mrheltic/Logger/medias/doc-esp32-pinout-reference-wroom-devkit.png

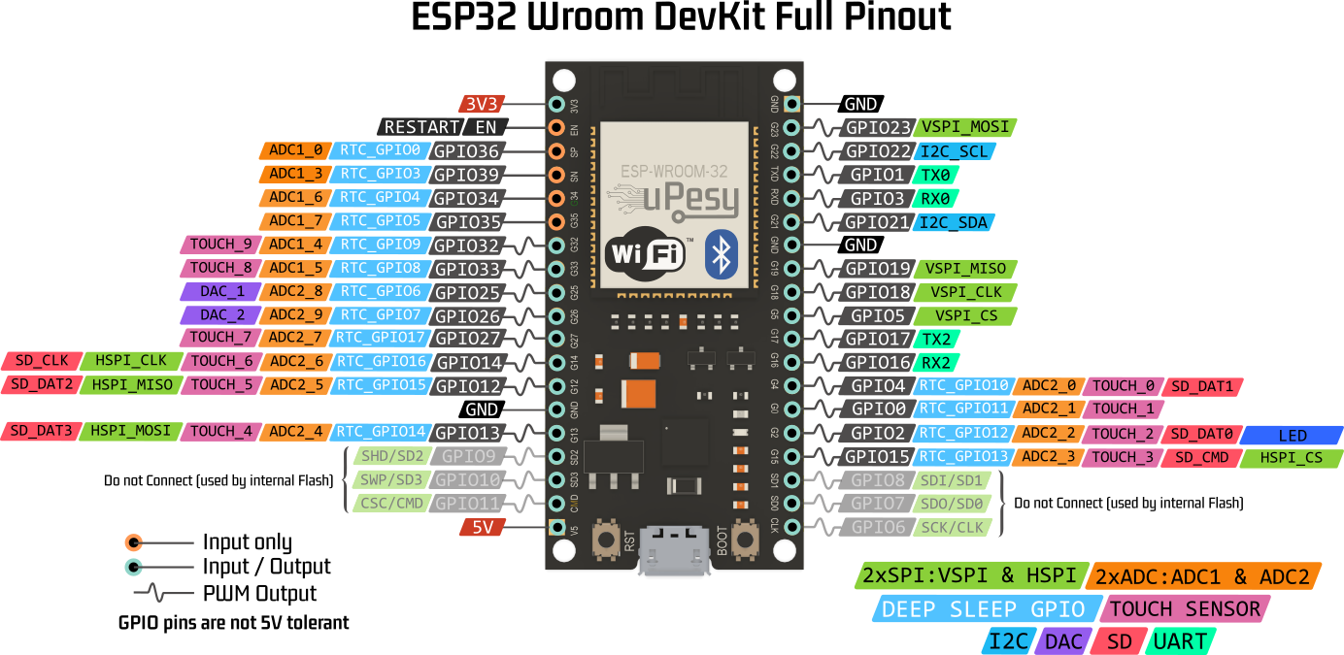
medias/doc-esp32-pinout-reference-wroom-devkit.png
