mrheltic/Logger/medias/kicad_logger_circuit.jpg

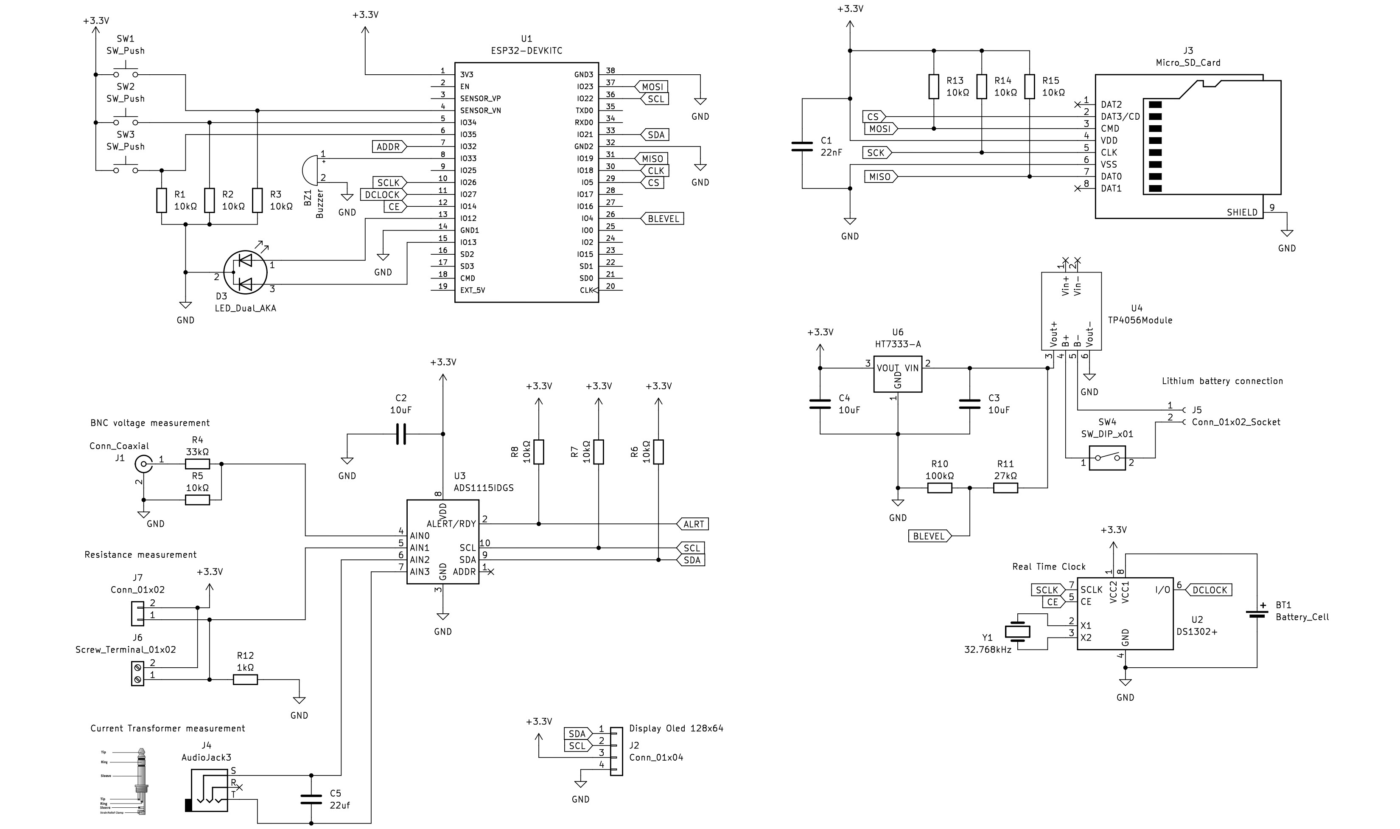
medias/kicad_logger_circuit.jpg
