mrheltic/Logger/medias/pcb_preview_bottom.png

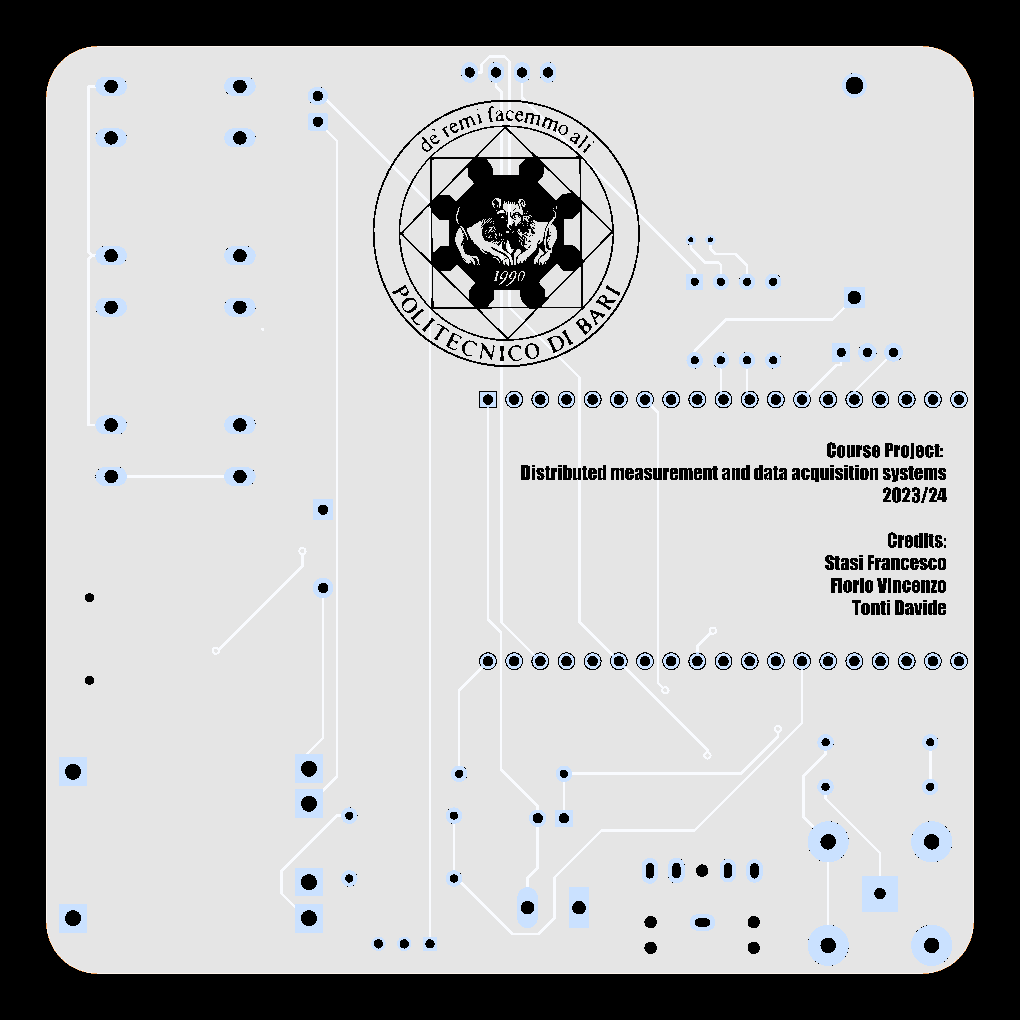
medias/pcb_preview_bottom.png
