mrheltic/Logger/medias/pcb_preview_top.png

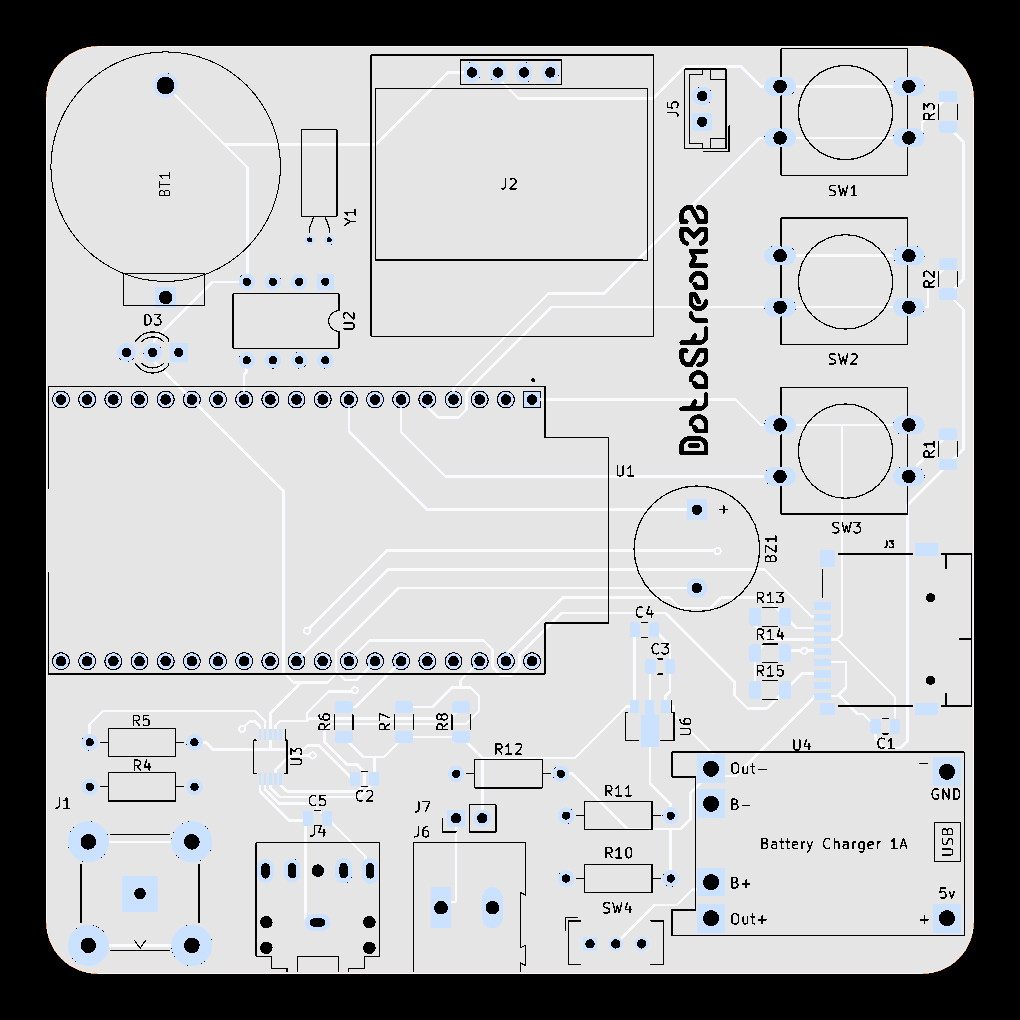
medias/pcb_preview_top.png
