mrheltic/Logger/Performance/Calibration/calibration.png

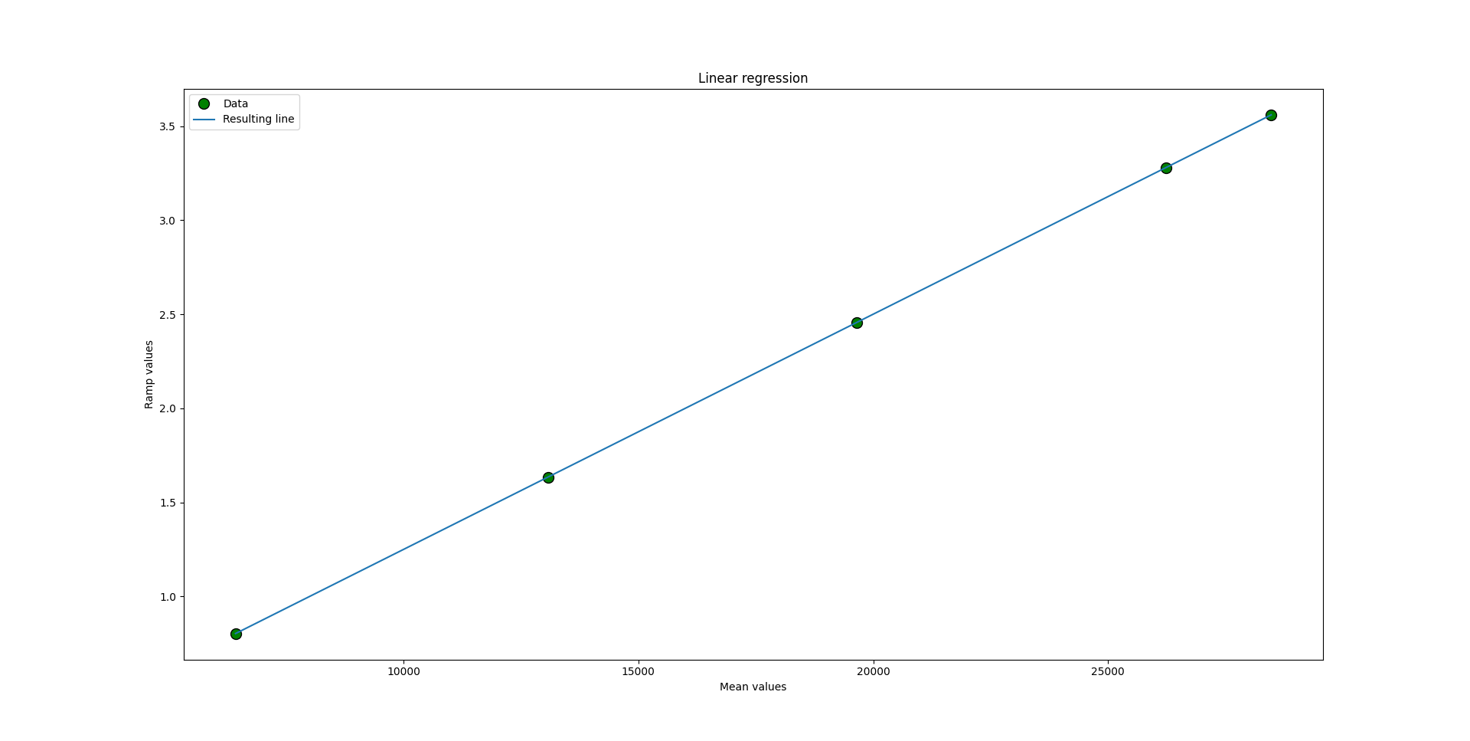
Performance/Calibration/calibration.png
