mrheltic/Logger/Performance/Fft/rampfft2.png

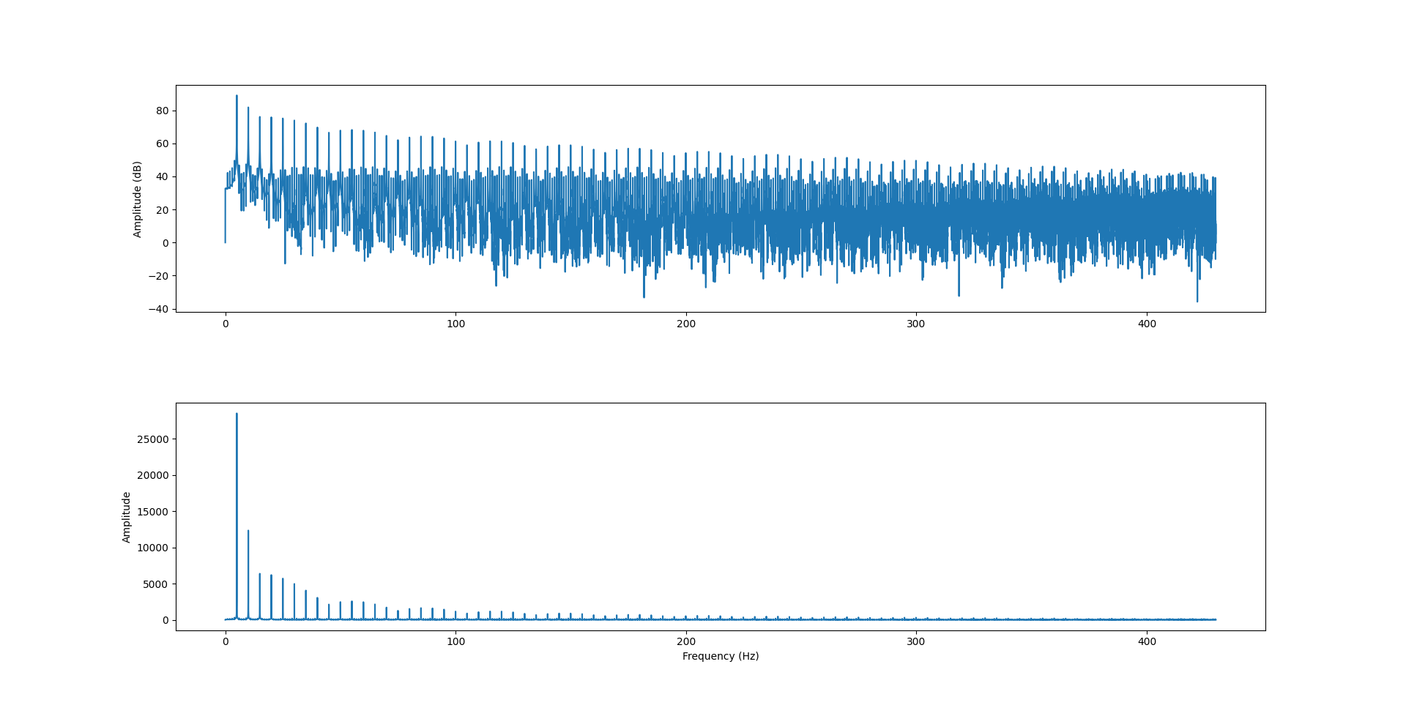
Performance/Fft/rampfft2.png
