mrheltic/Logger/Performance/Fft/sinusoidalfft1.png

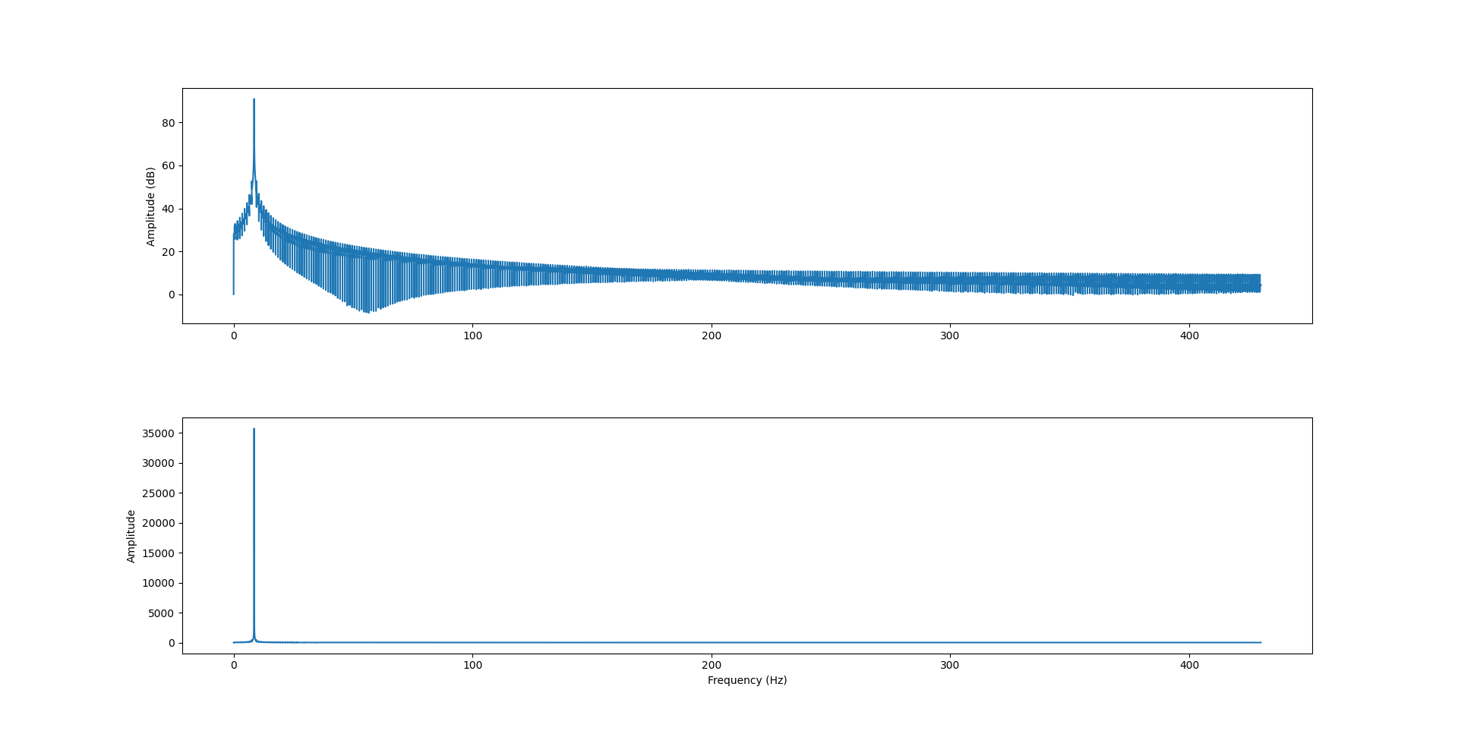
Performance/Fft/sinusoidalfft1.png
