mrheltic/Logger/Performance/Fft/sinusoidalfft2.png

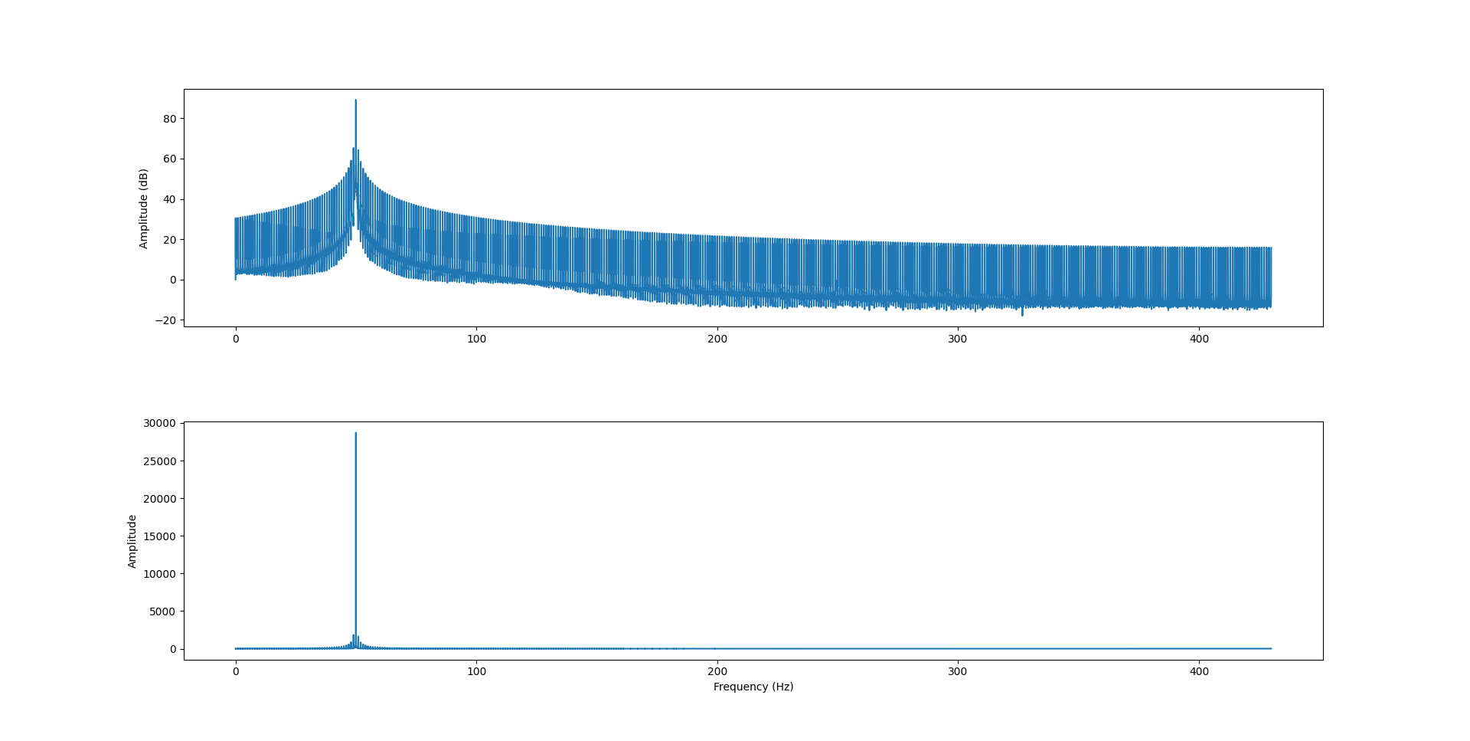
Performance/Fft/sinusoidalfft2.png
