mrheltic/Logger/Performance/Fft/sinusoidalfft4.png

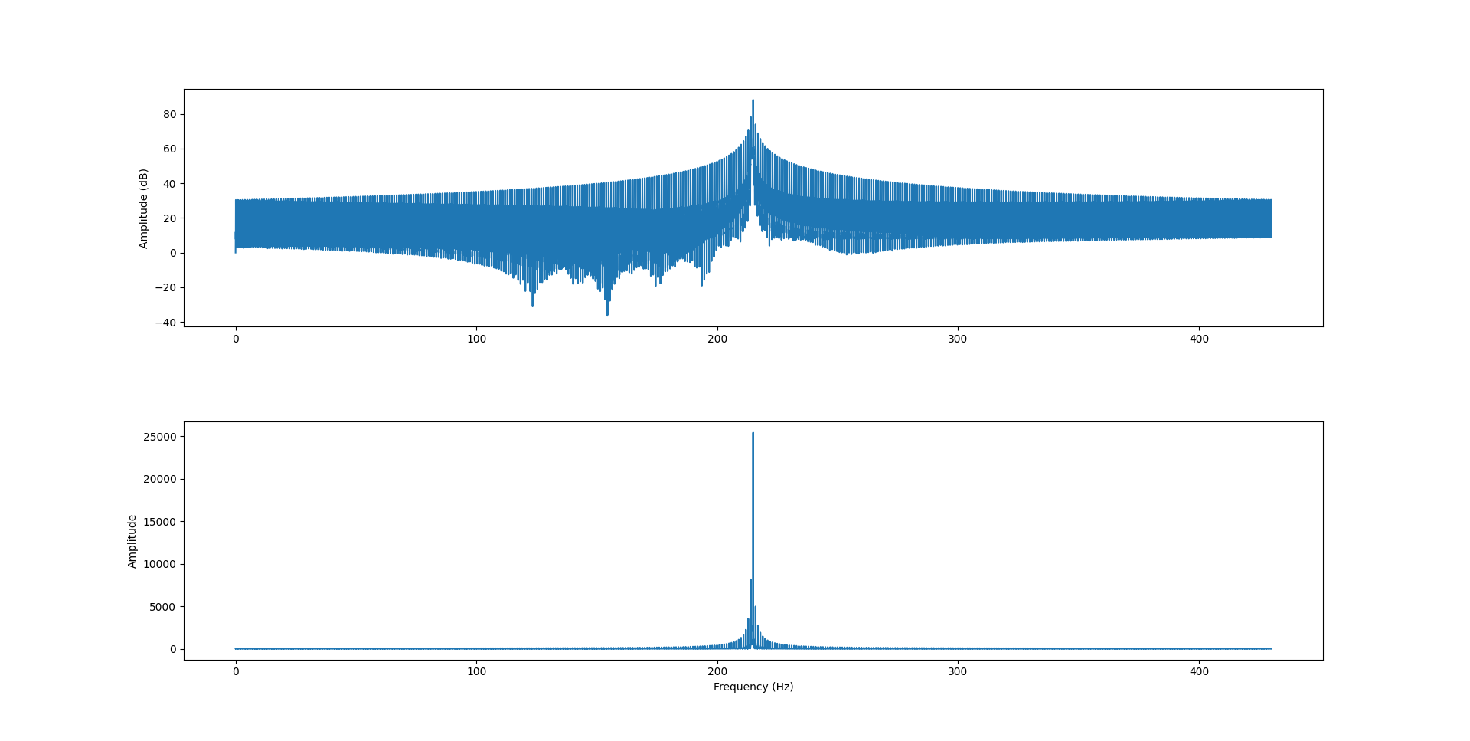
Performance/Fft/sinusoidalfft4.png
