mrheltic/Logger/Performance/Fft/sinusoidalfft6.png

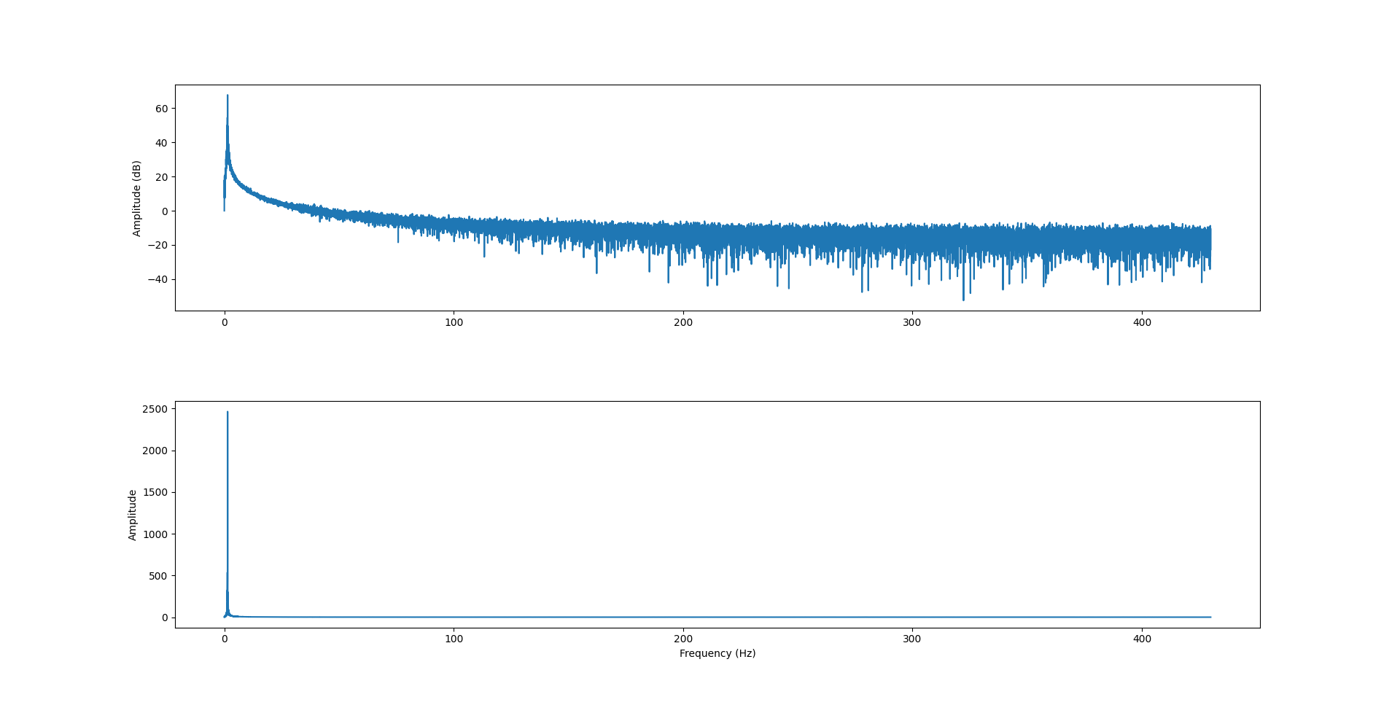
Performance/Fft/sinusoidalfft6.png
