mrheltic/Logger/Performance/Fft/sinusoidalfft8.png

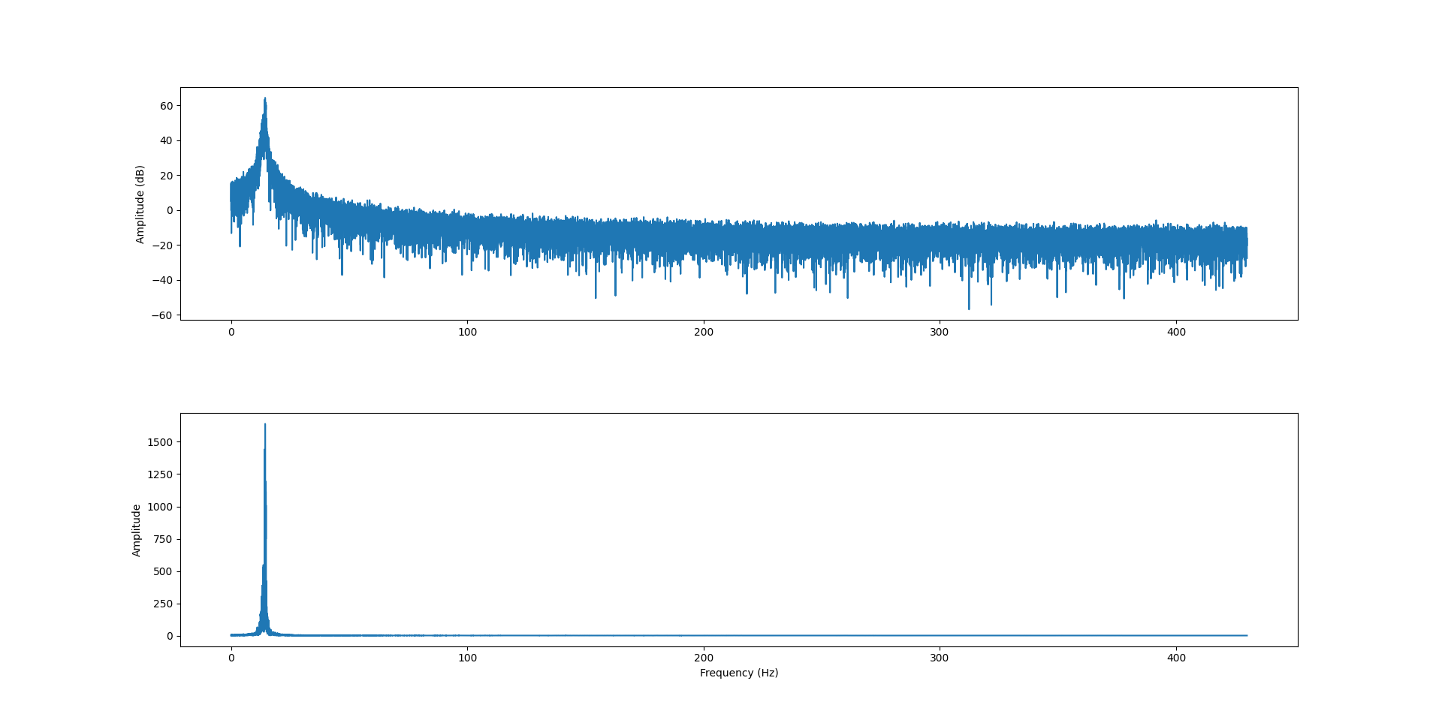
Performance/Fft/sinusoidalfft8.png
