mrheltic/Logger/Performance/Fft/sinusoidalfft9.png

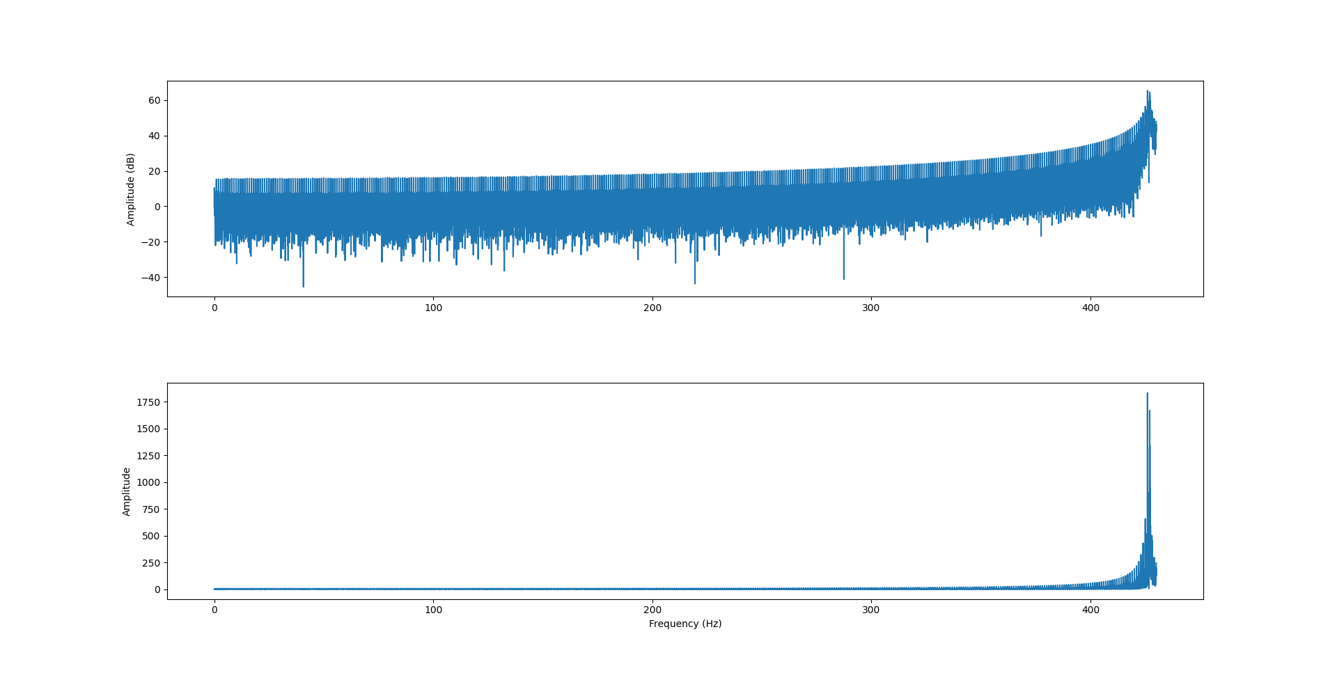
Performance/Fft/sinusoidalfft9.png
