mrheltic/Logger/Performance/Noise/floatingnoise.png

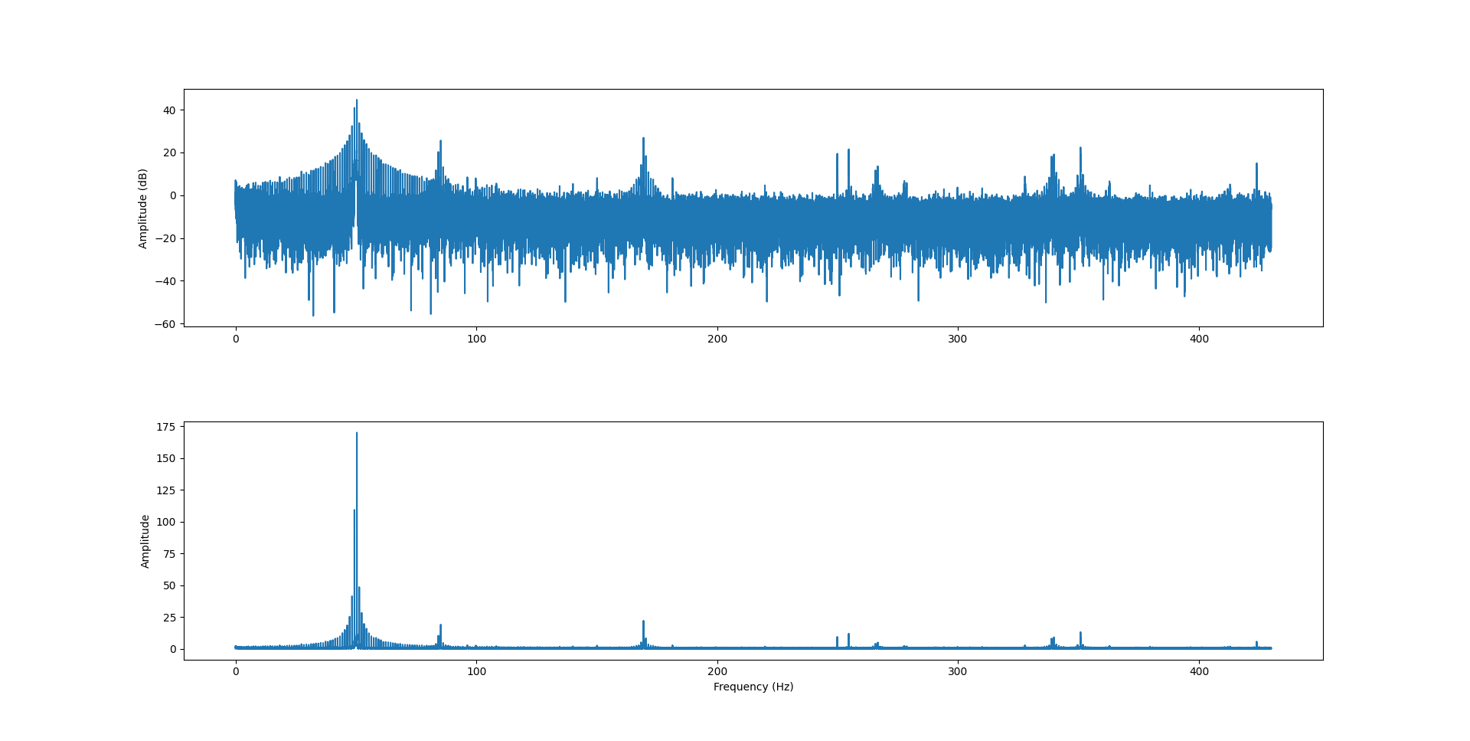
Performance/Noise/floatingnoise.png
