mrheltic/Logger/Performance/Noise/shortingnoise.png

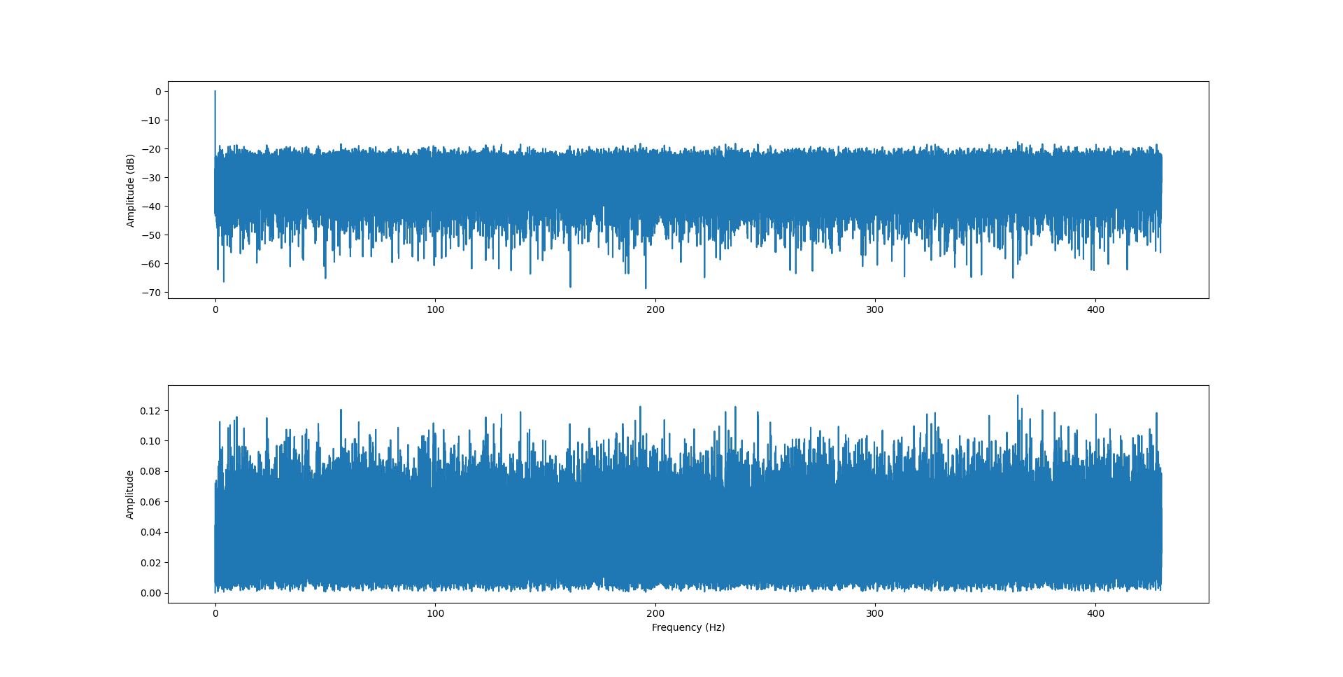
Performance/Noise/shortingnoise.png
