mrheltic/Logger/Performance/Ramp/rampfit1.png

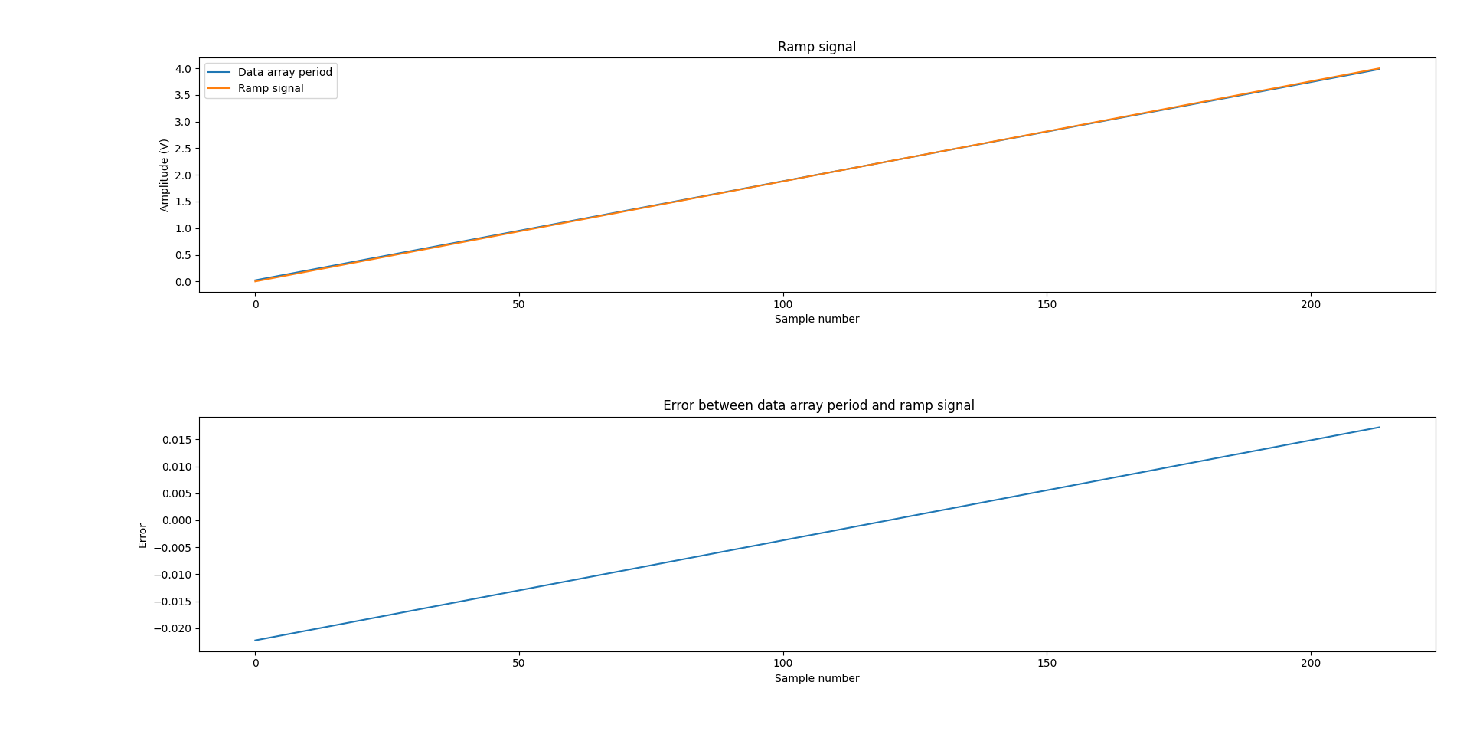
Performance/Ramp/rampfit1.png
