mrheltic/Logger/Performance/Ramp/rampfsr1.png

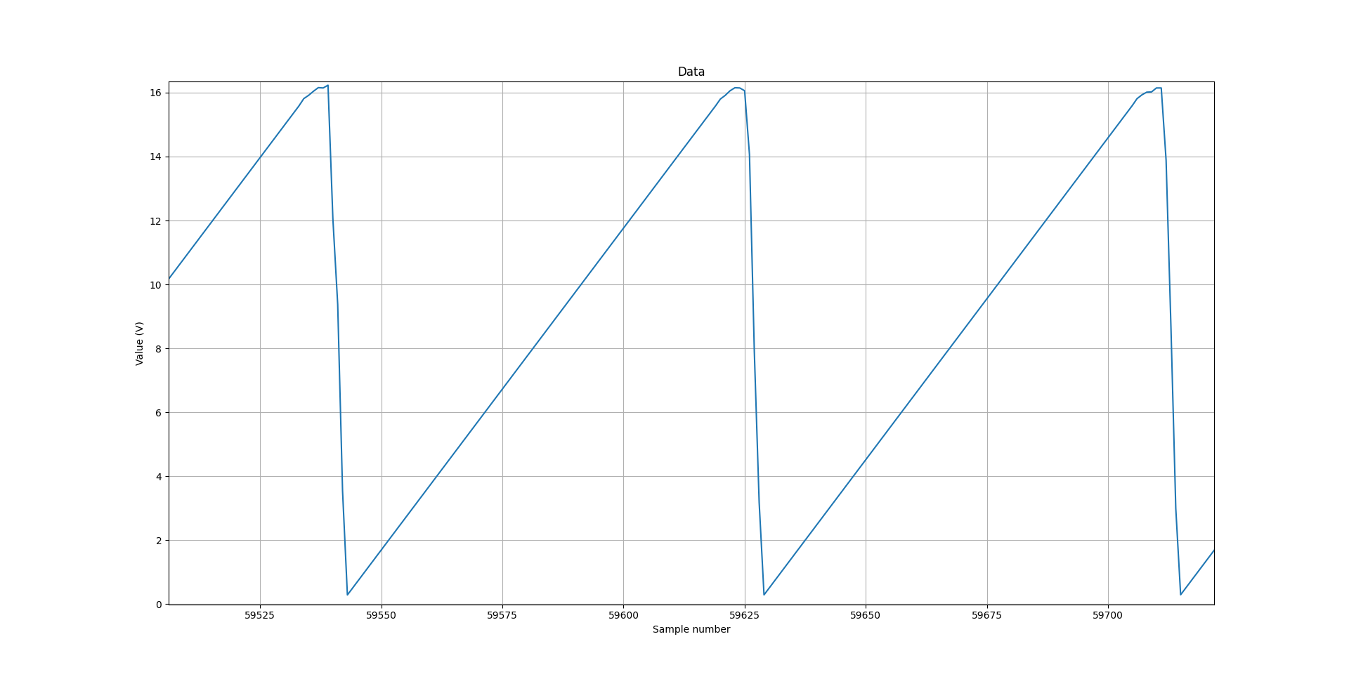
Performance/Ramp/rampfsr1.png
