mrheltic/Logger/Performance/Ramp/rampfsr2.png

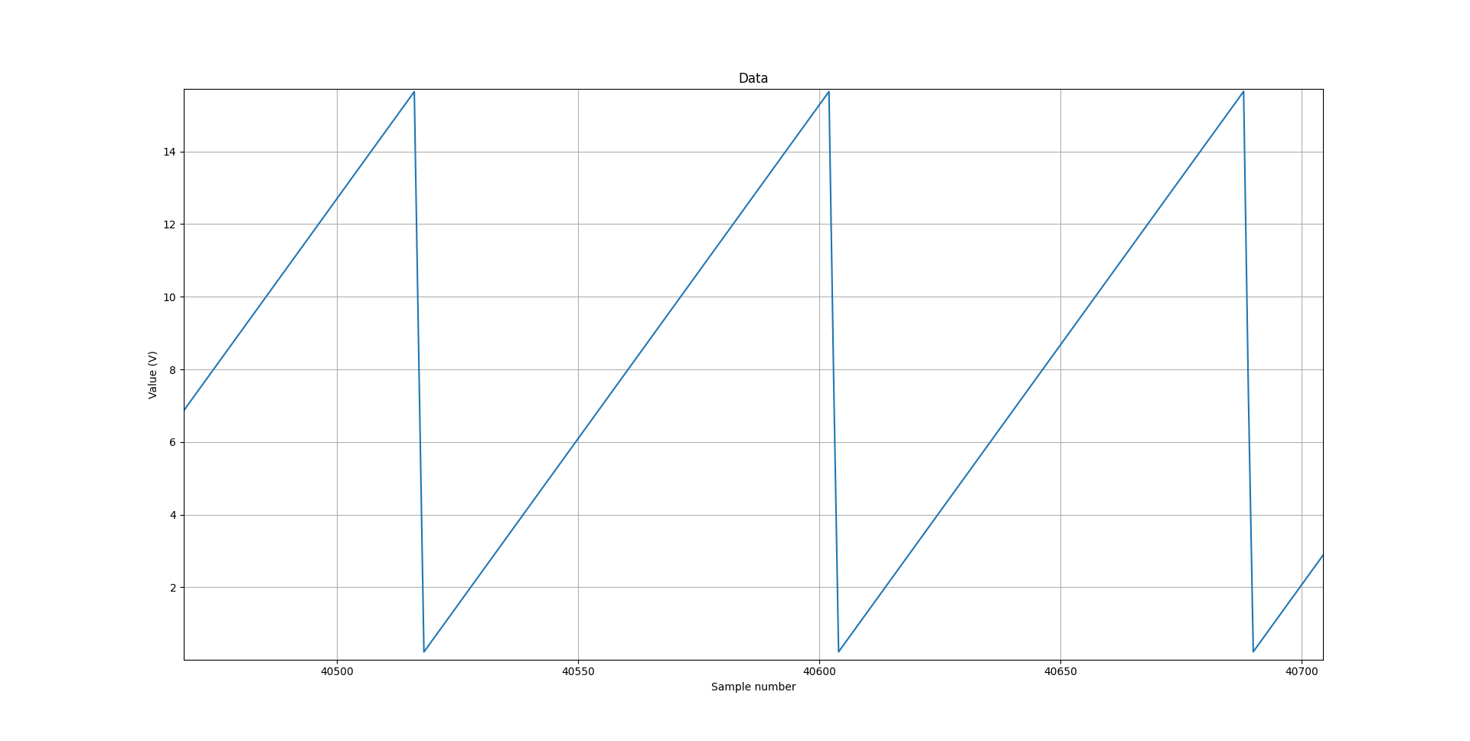
Performance/Ramp/rampfsr2.png
