mrheltic/Logger/Performance/Ramp/rampfsr3.png

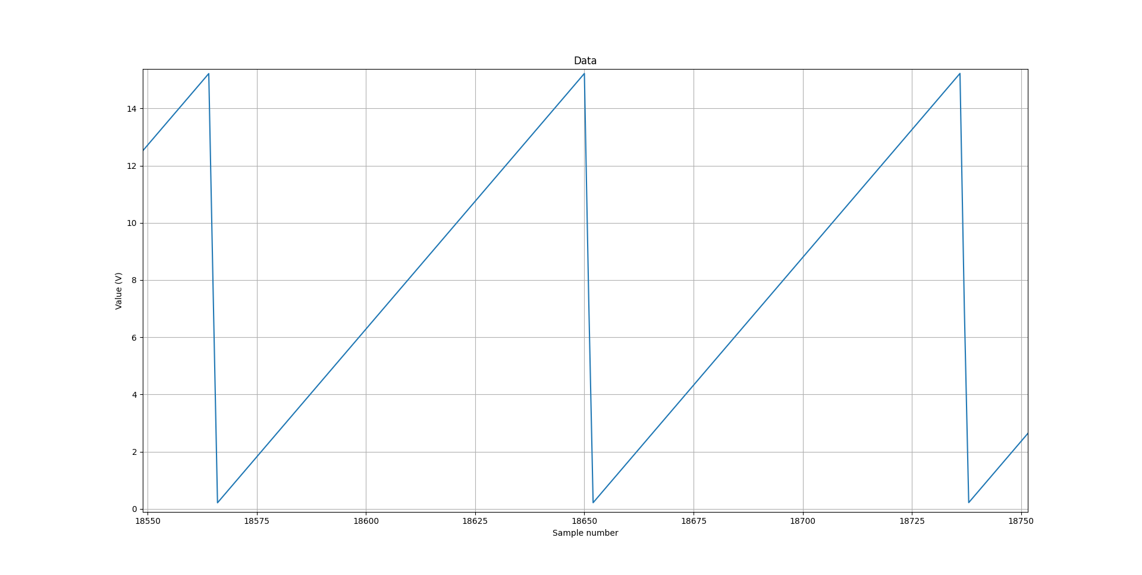
Performance/Ramp/rampfsr3.png
