mrheltic/Logger/Performance/Ramp/rampmeanstd1.png

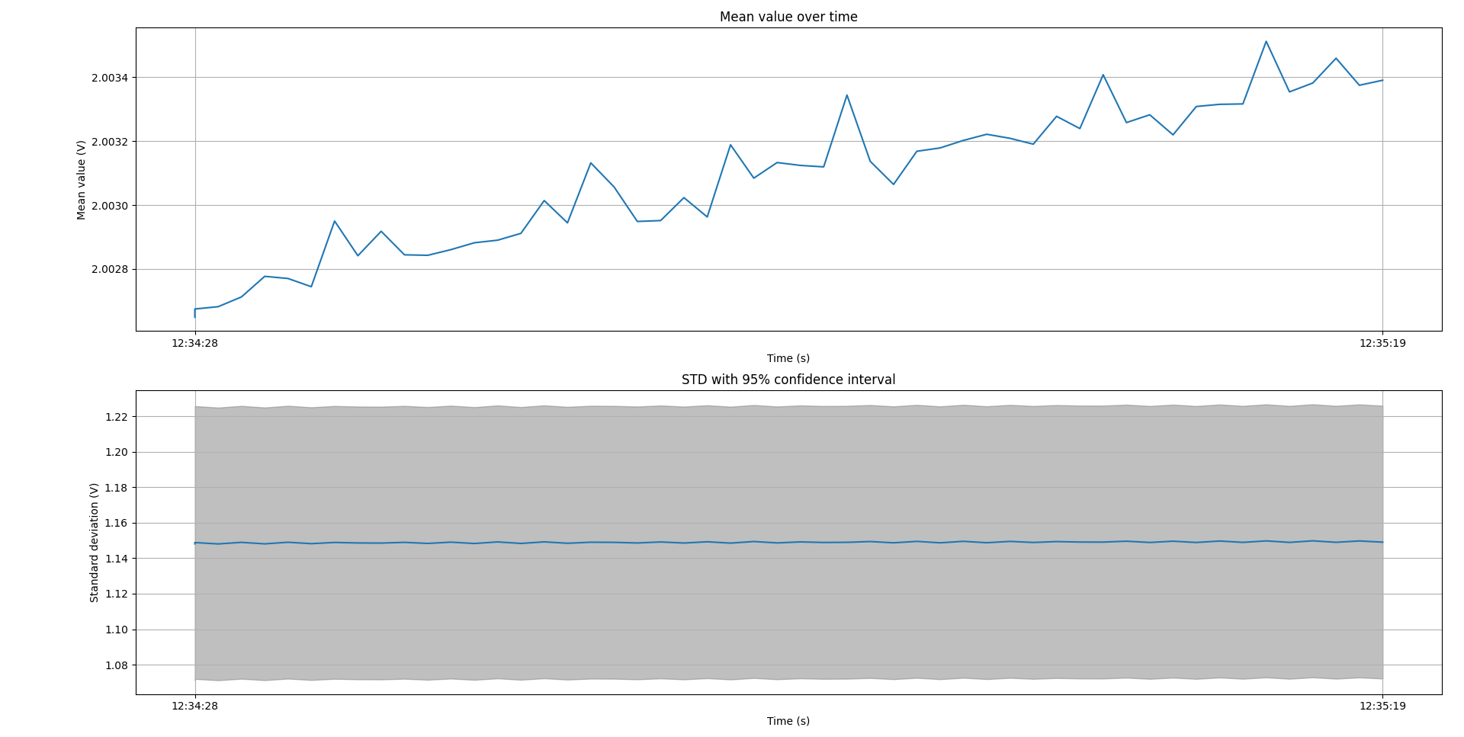
Performance/Ramp/rampmeanstd1.png
