mrheltic/Logger/Performance/Ramp/rampvalue1.png

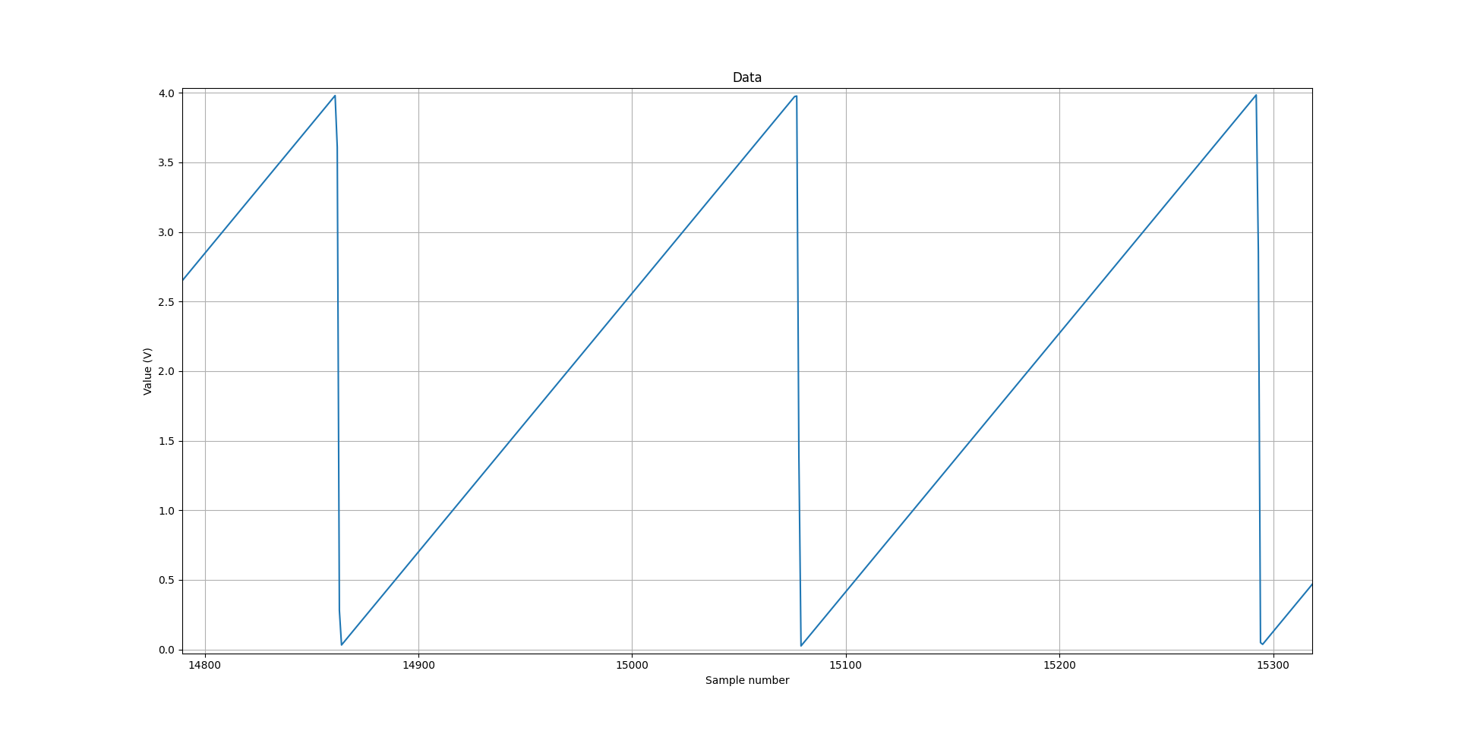
Performance/Ramp/rampvalue1.png
