mrheltic/Logger/Performance/Ramp/rampvalue2.png

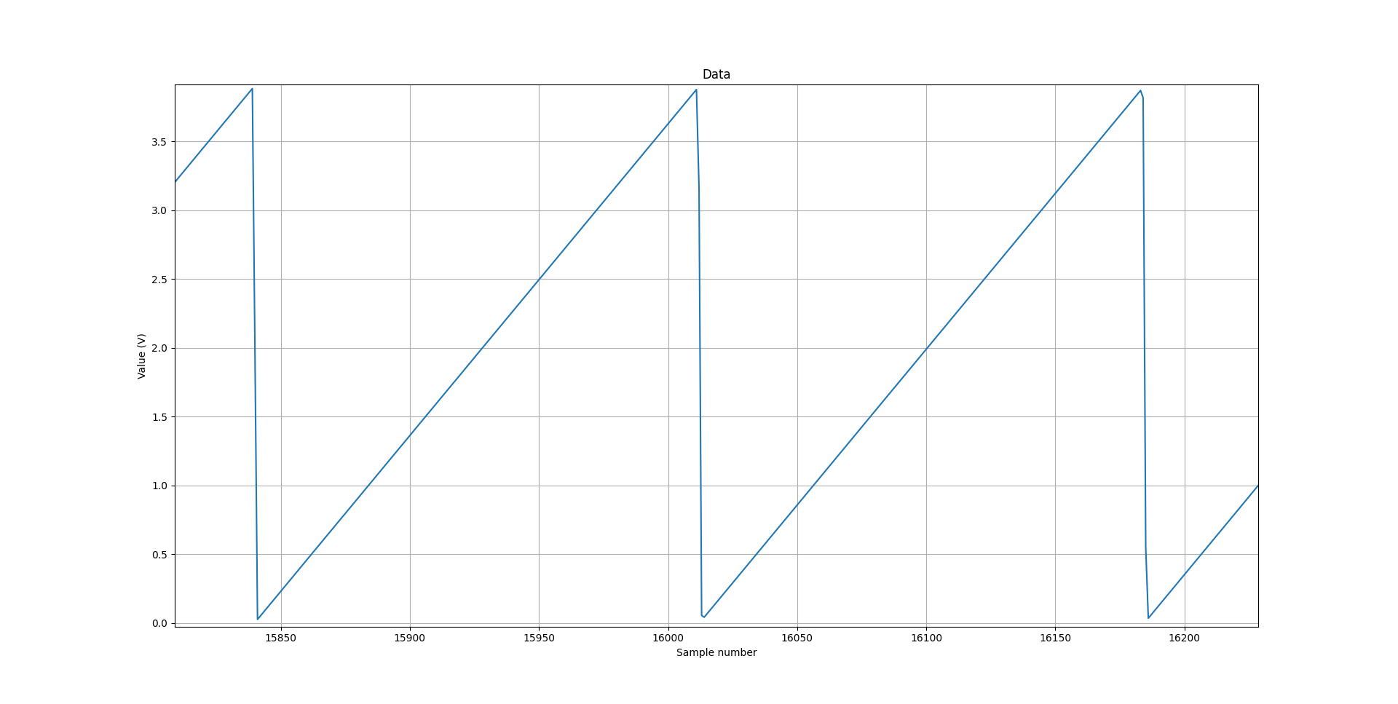
Performance/Ramp/rampvalue2.png
