mrheltic/Logger/Performance/Sinusoidal/sinusoidalmeanstd1.png

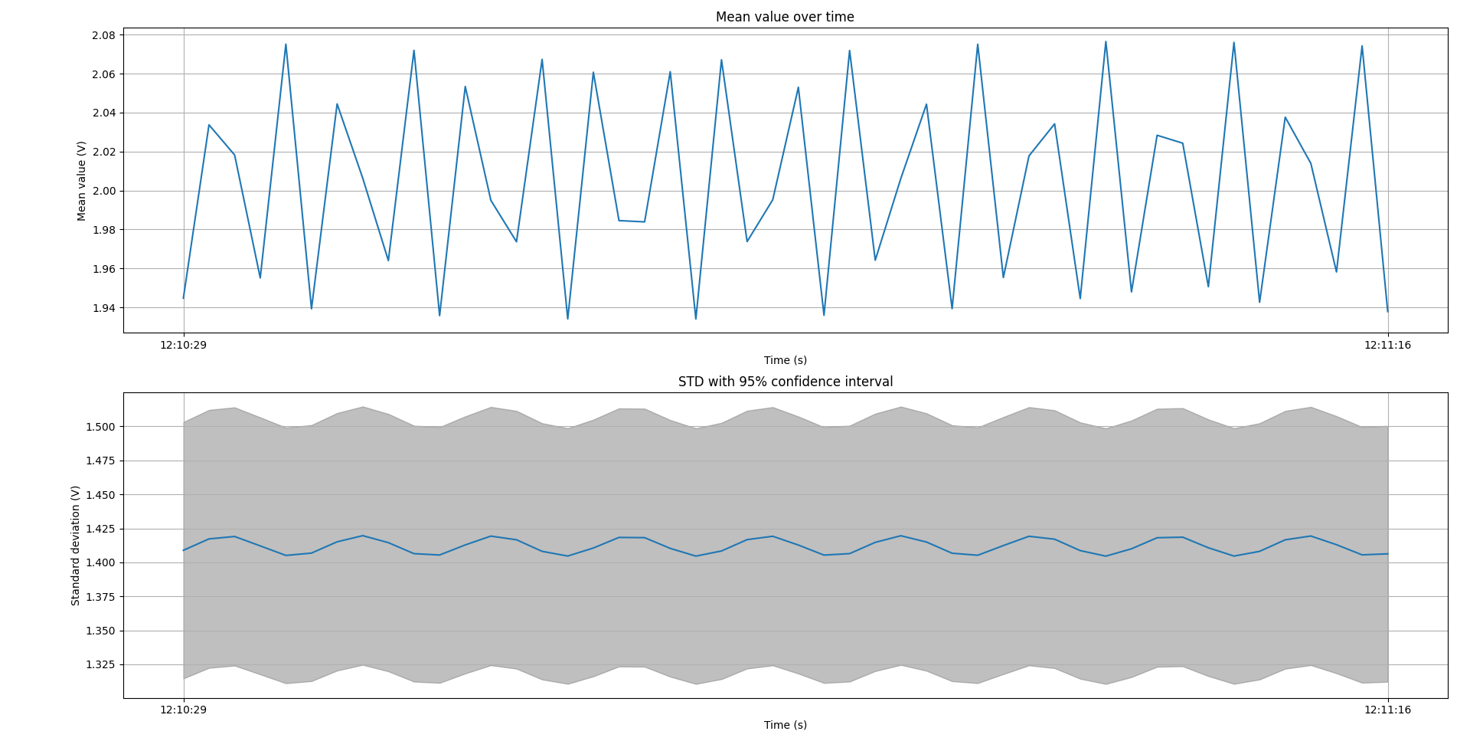
Performance/Sinusoidal/sinusoidalmeanstd1.png
