mrheltic/Logger/Performance/Sinusoidal/sinusoidalmeanstd2.png

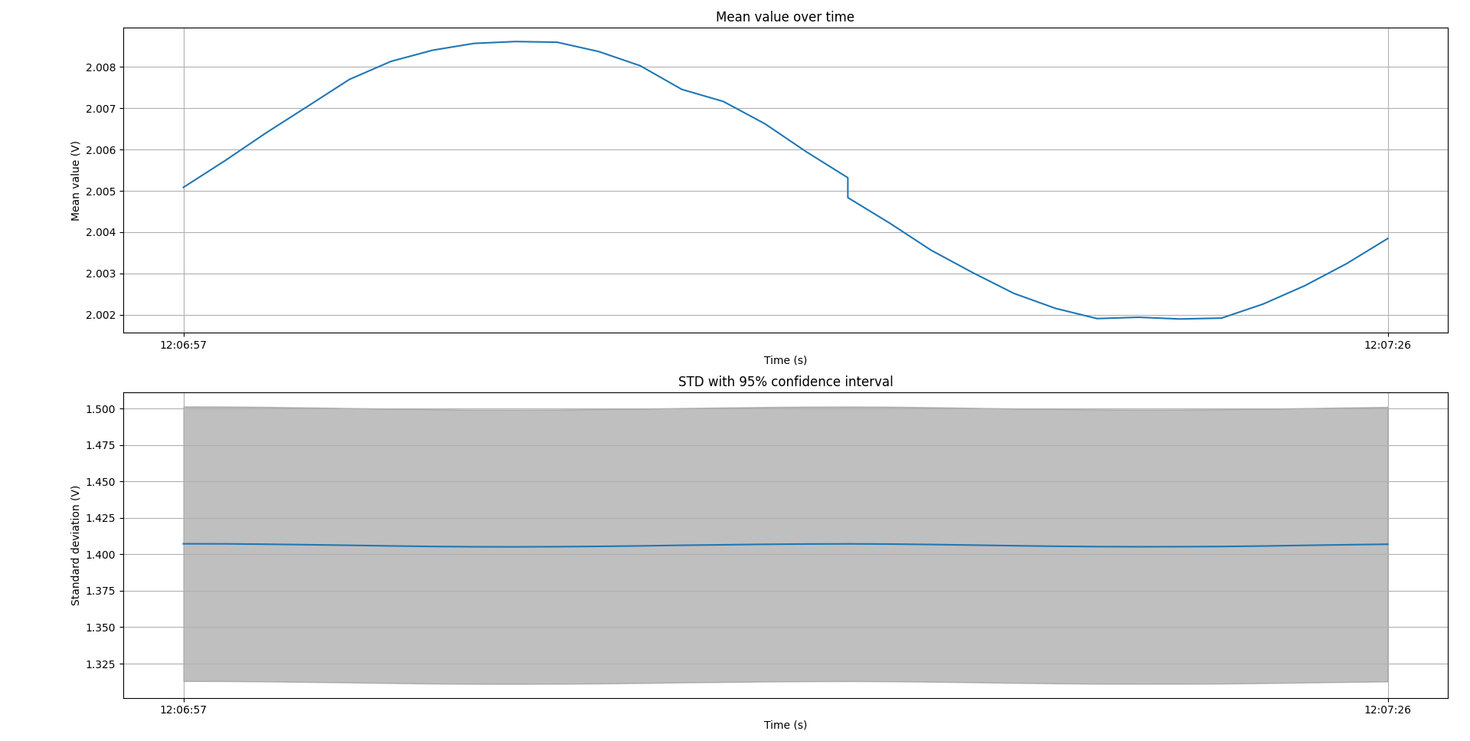
Performance/Sinusoidal/sinusoidalmeanstd2.png
