mrheltic/Logger/Performance/Sinusoidal/sinusoidalmeanstd3.png

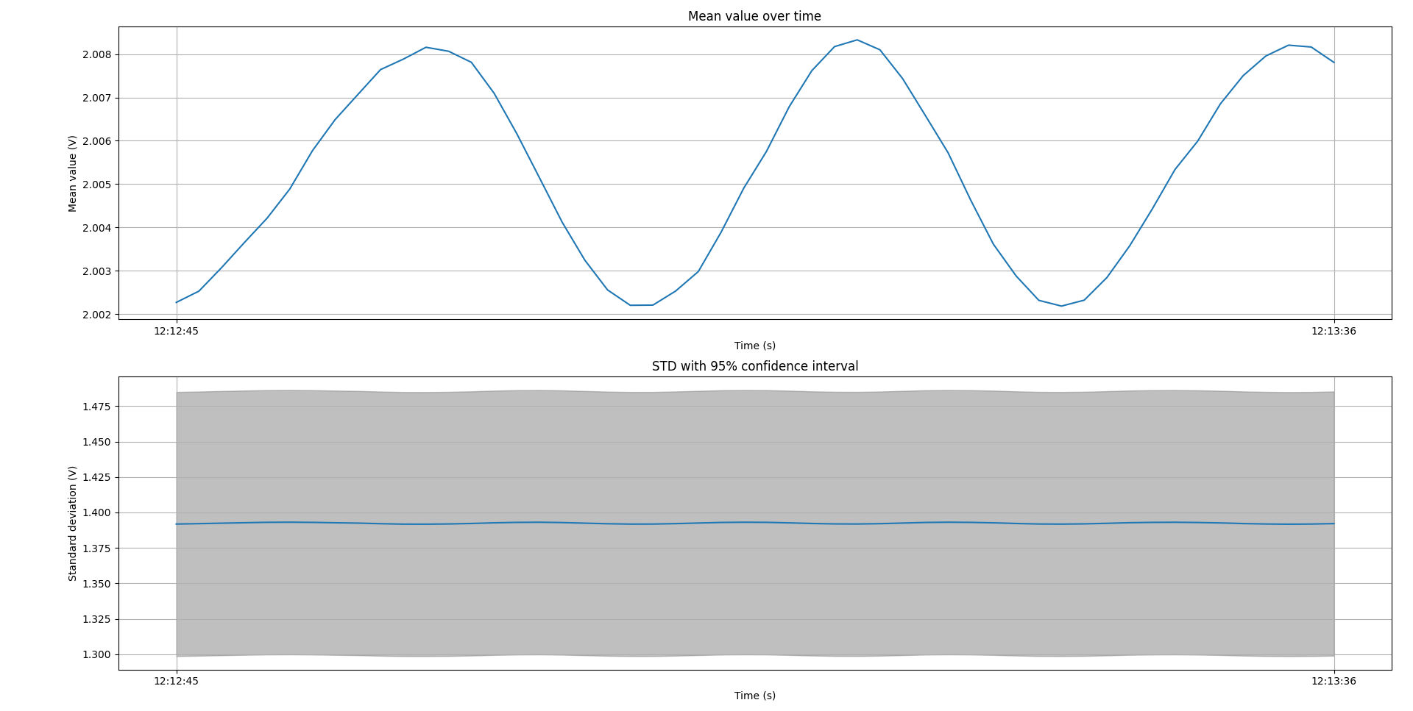
Performance/Sinusoidal/sinusoidalmeanstd3.png
