mrheltic/Logger/Performance/Sinusoidal/sinusoidalmeanstd4.png

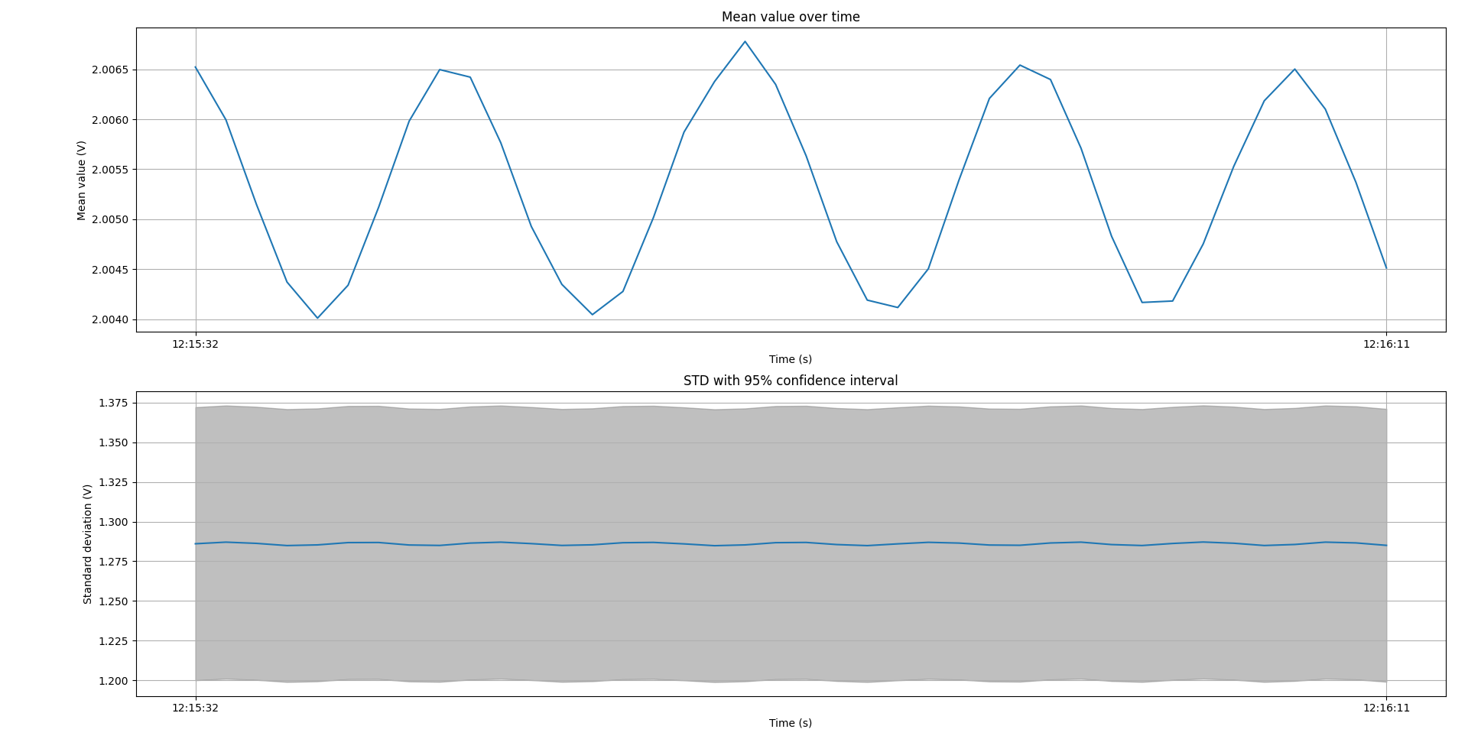
Performance/Sinusoidal/sinusoidalmeanstd4.png
