mrheltic/Logger/Performance/Sinusoidal/sinusoidalmeanstd5.png

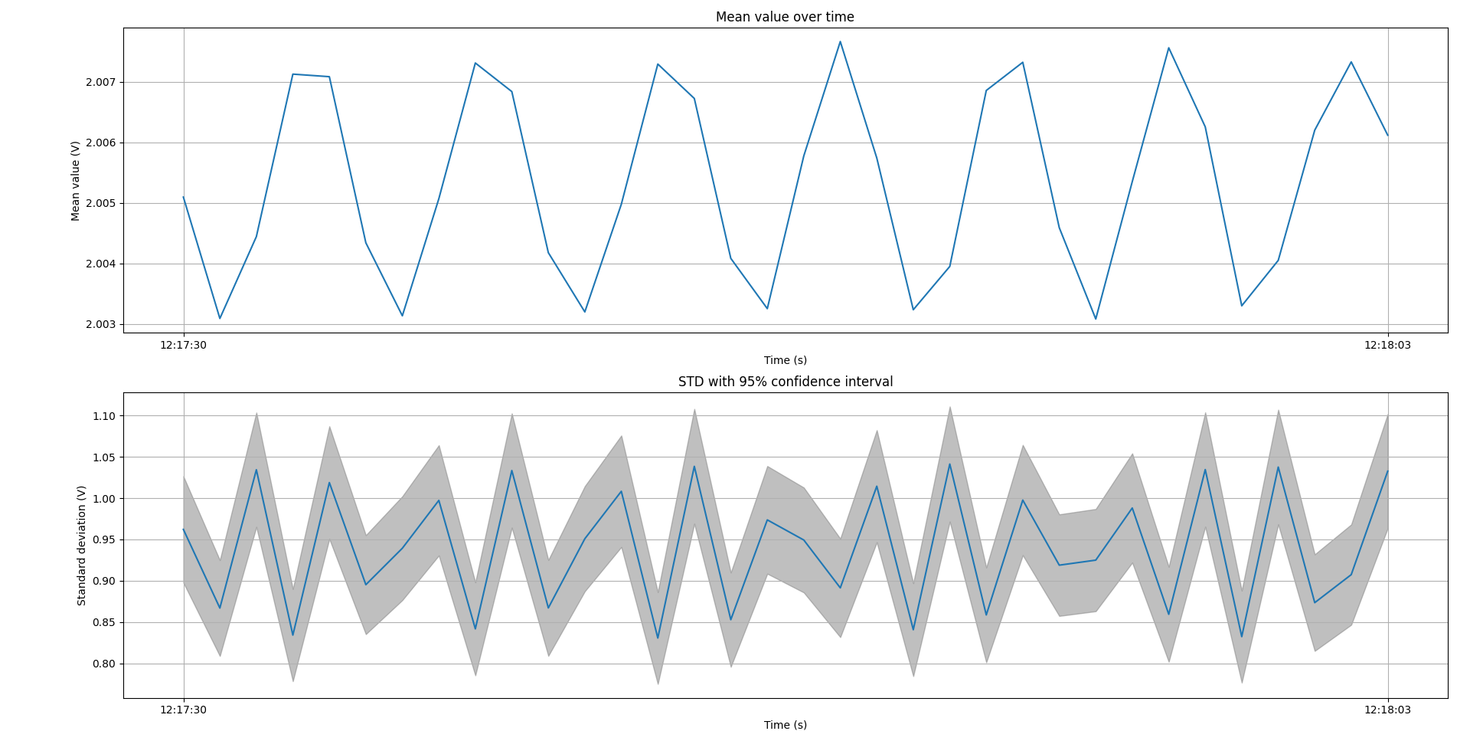
Performance/Sinusoidal/sinusoidalmeanstd5.png
