mrheltic/Logger/Performance/Sinusoidal/sinusoidalmeanstd6.png

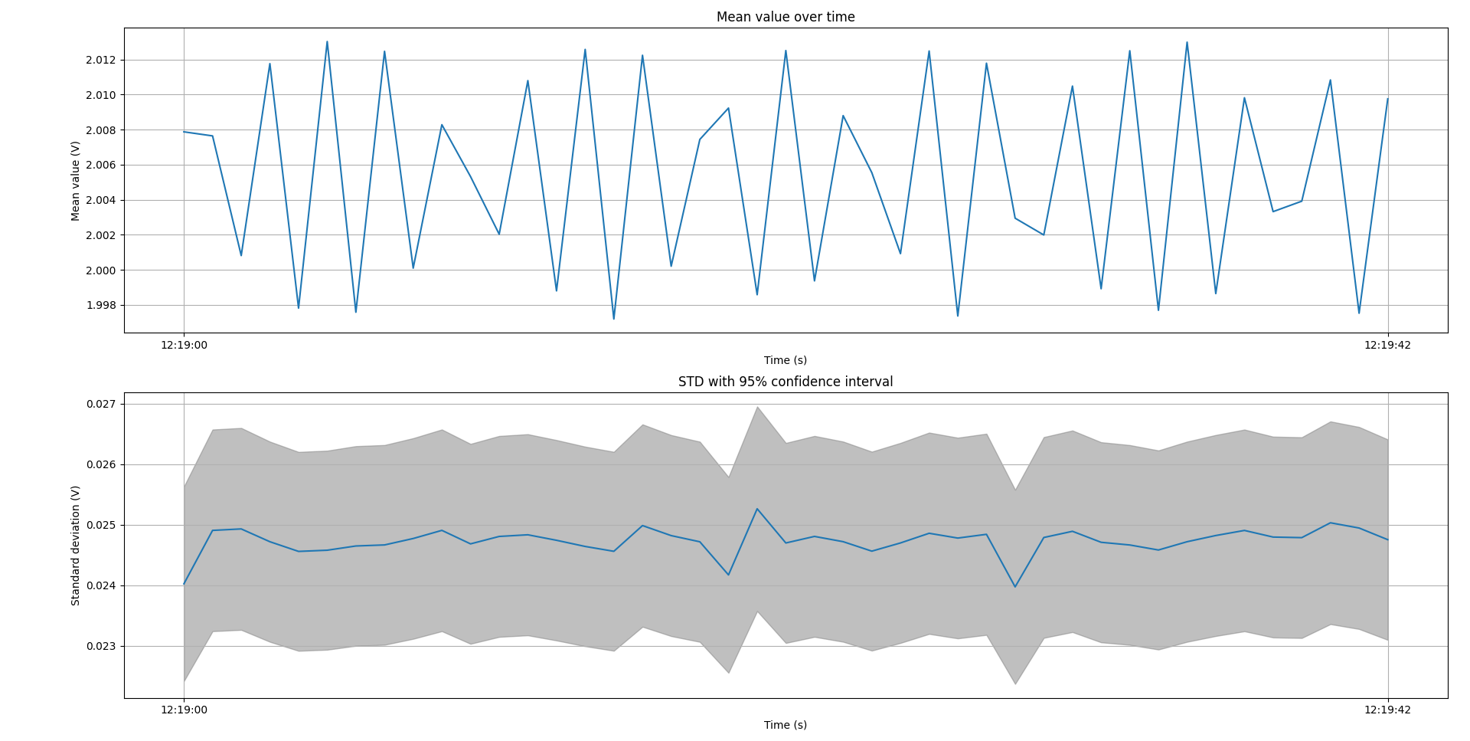
Performance/Sinusoidal/sinusoidalmeanstd6.png
