mrheltic/Logger/Performance/Sinusoidal/sinusoidalmeanstd7.png

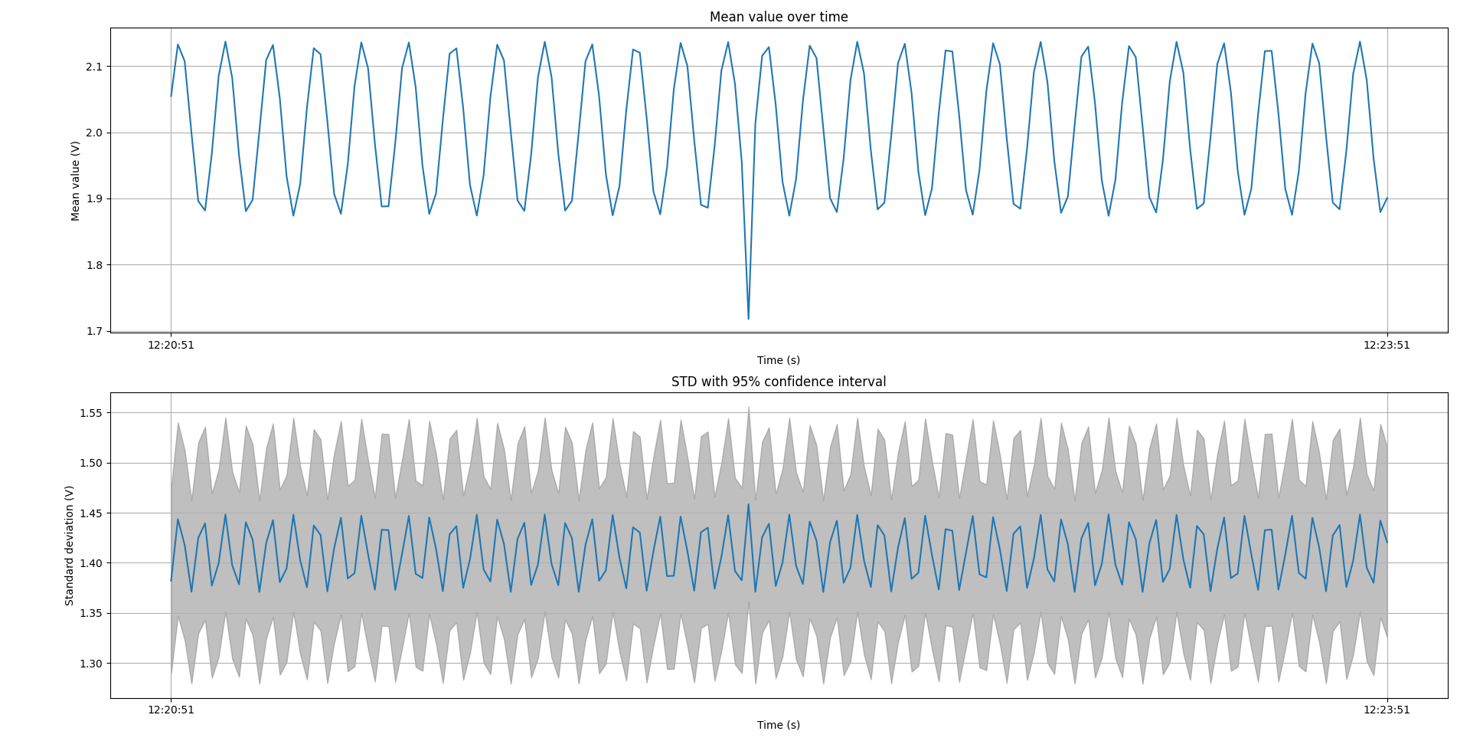
Performance/Sinusoidal/sinusoidalmeanstd7.png
