mrheltic/Logger/Performance/Sinusoidal/sinusoidalmeanstd8.png

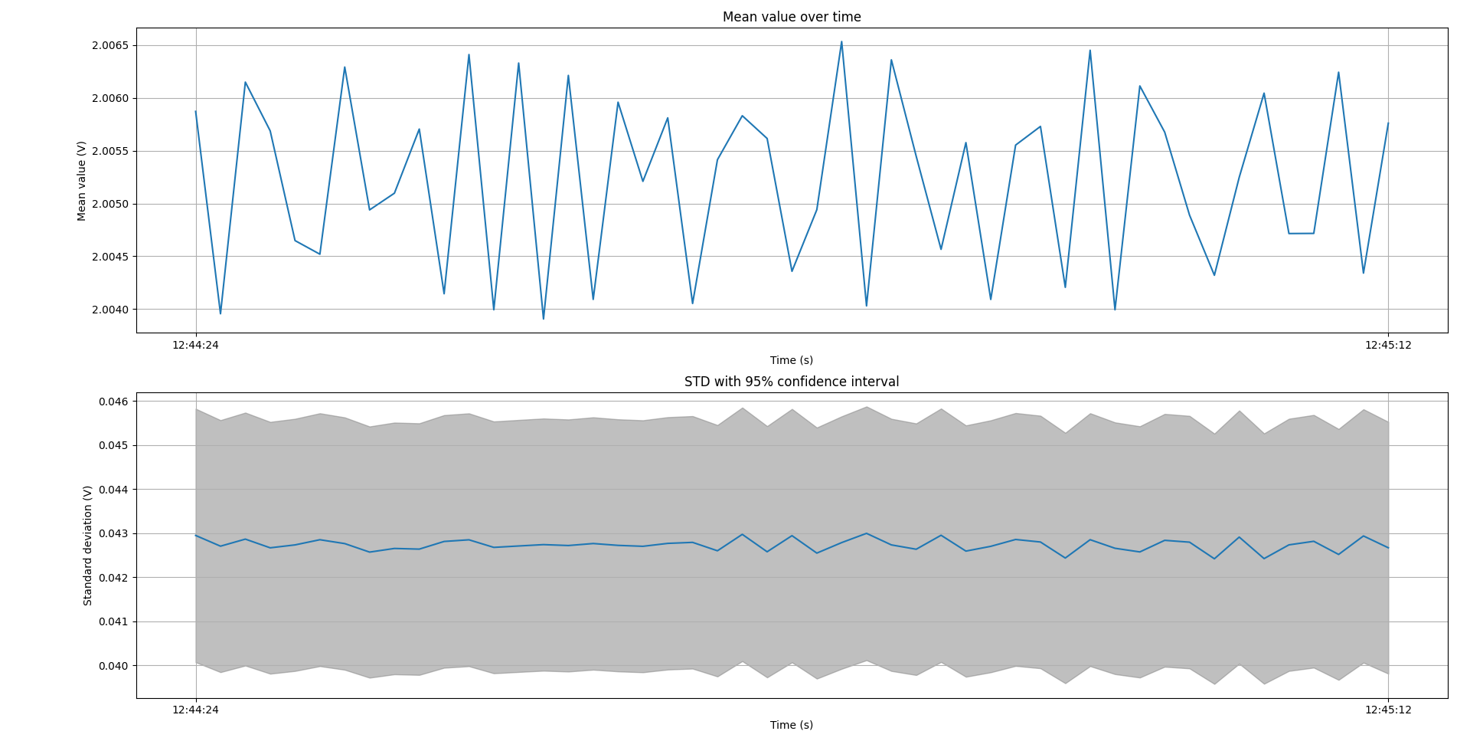
Performance/Sinusoidal/sinusoidalmeanstd8.png
