mrheltic/Logger/Performance/Sinusoidal/sinusoidalmeanstd9.png

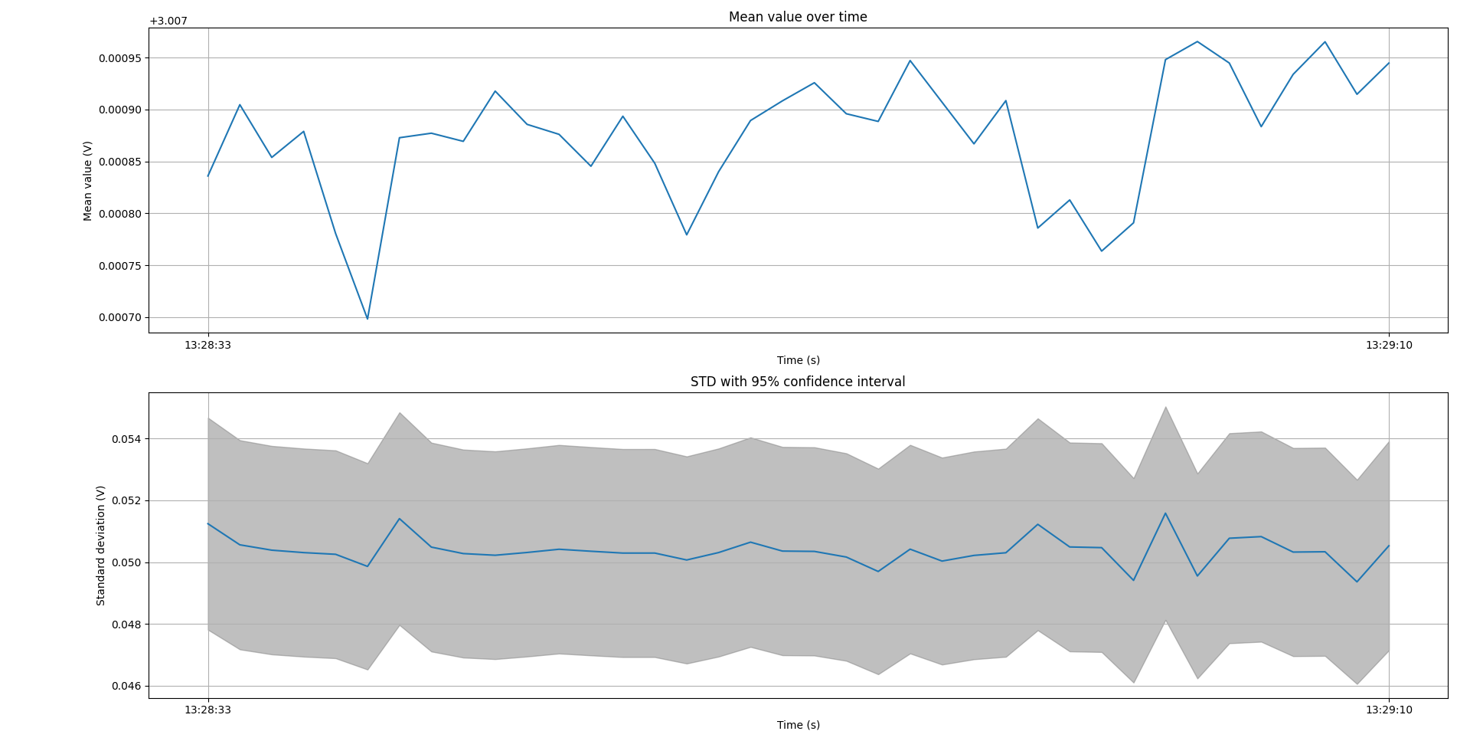
Performance/Sinusoidal/sinusoidalmeanstd9.png
