mrheltic/Logger/Performance/Sinusoidal/sinusoidalvalue1.png

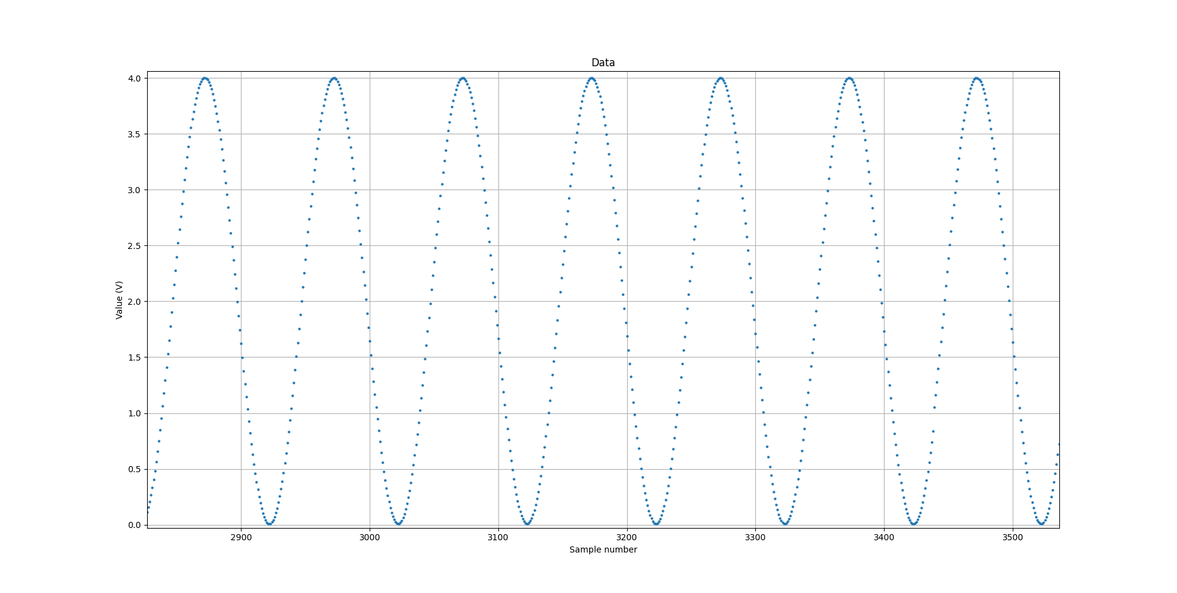
Performance/Sinusoidal/sinusoidalvalue1.png
