mrheltic/Logger/Performance/Sinusoidal/sinusoidalvalue2.png

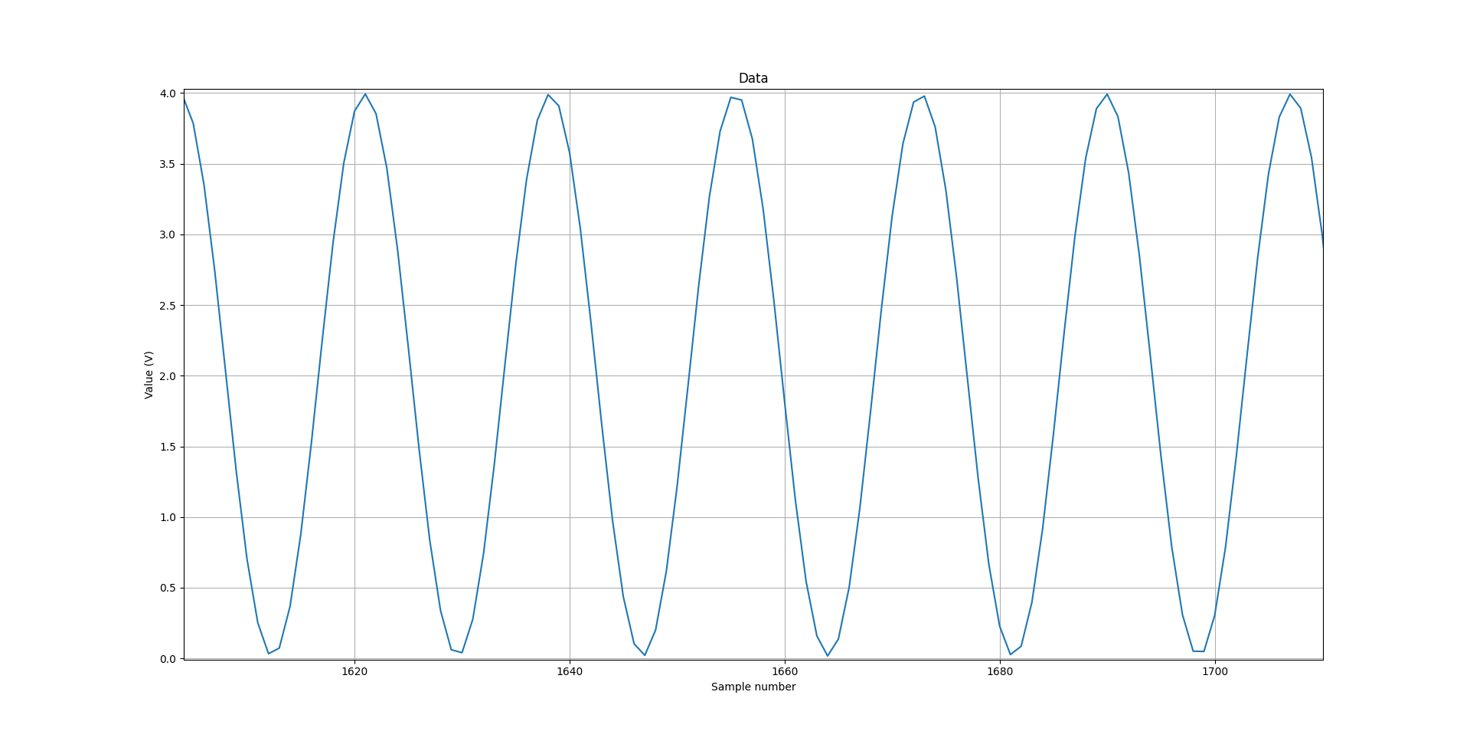
Performance/Sinusoidal/sinusoidalvalue2.png
