mrheltic/Logger/Performance/Sinusoidal/sinusoidalvalue3.png

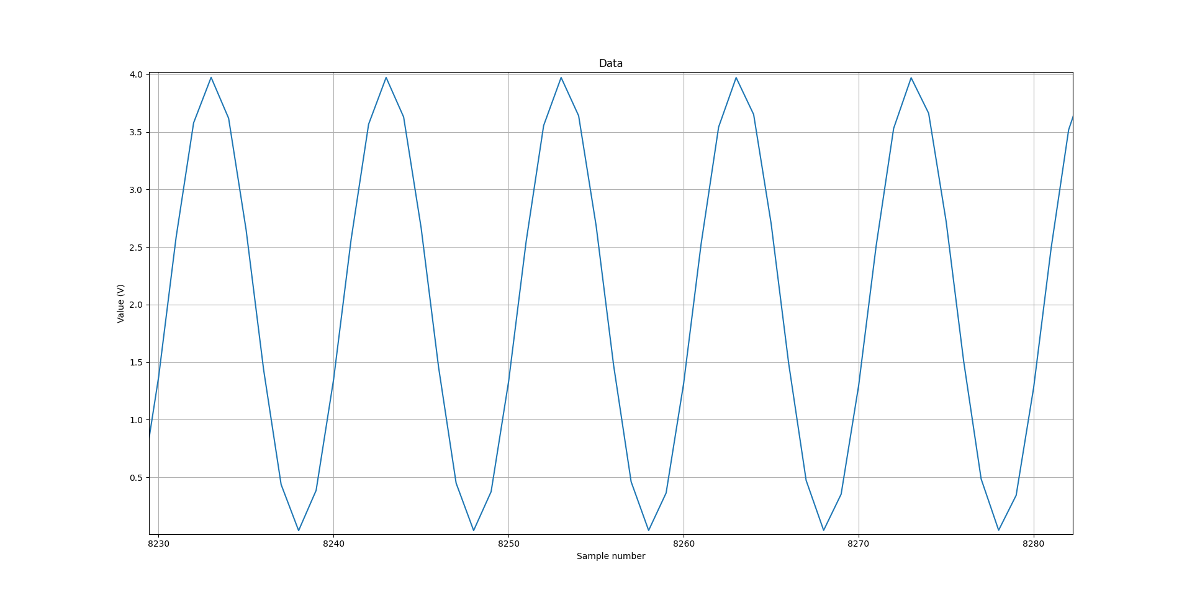
Performance/Sinusoidal/sinusoidalvalue3.png
