mrheltic/Logger/Performance/Sinusoidal/sinusoidalvalue4.png

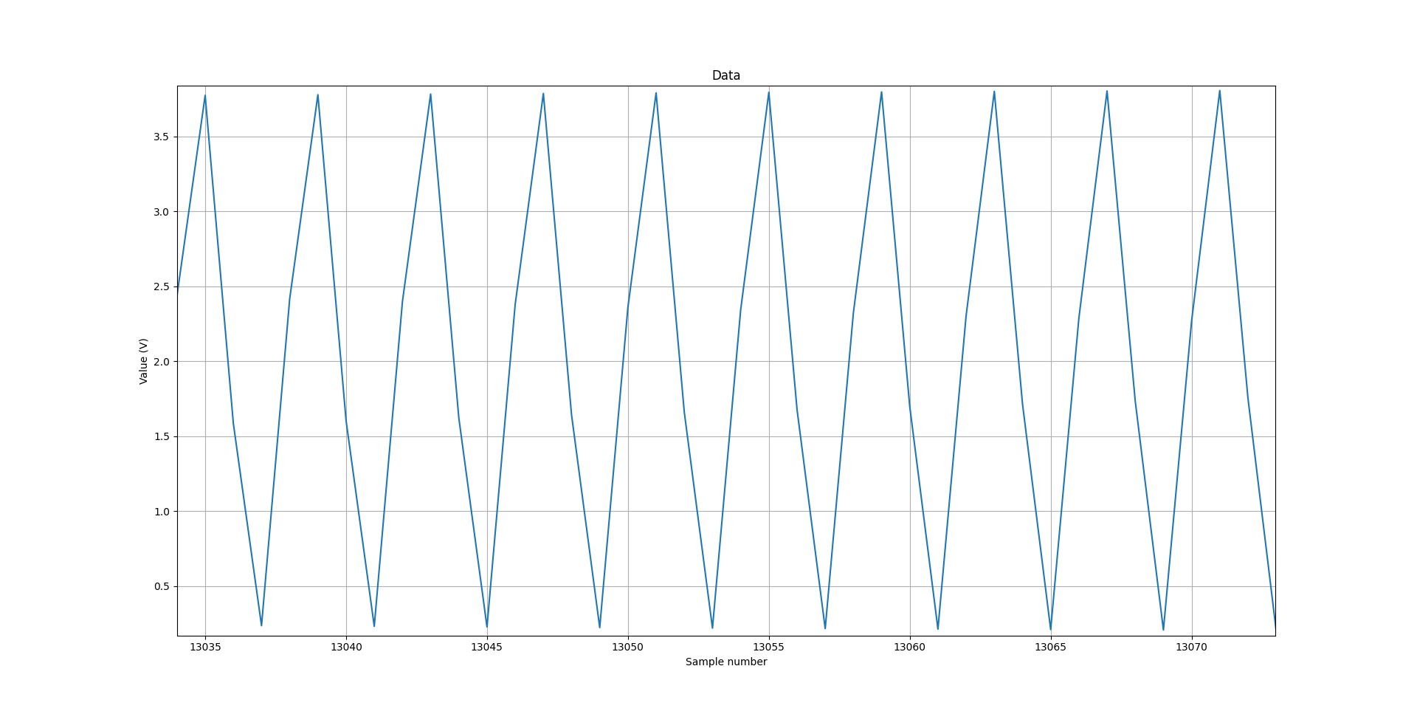
Performance/Sinusoidal/sinusoidalvalue4.png
