mrheltic/Logger/Performance/Sinusoidal/sinusoidalvalue5.png

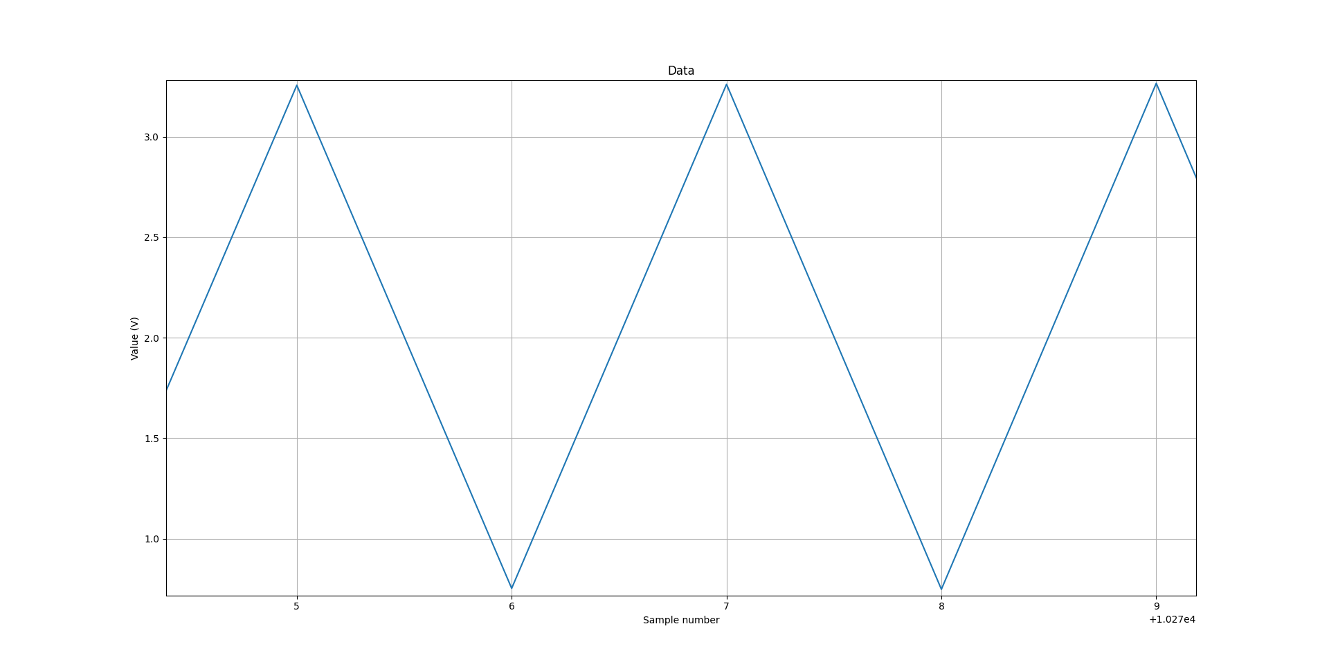
Performance/Sinusoidal/sinusoidalvalue5.png
