mrheltic/Logger/Performance/Sinusoidal/sinusoidalvalue6.png

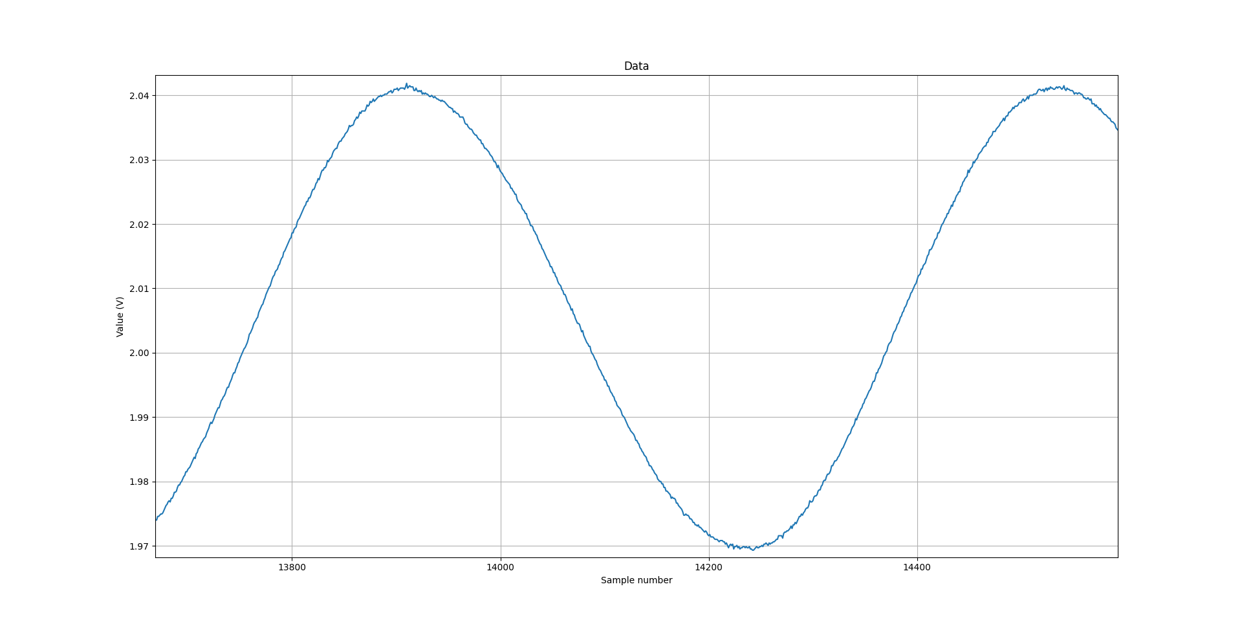
Performance/Sinusoidal/sinusoidalvalue6.png
