mrheltic/Logger/Performance/Sinusoidal/sinusoidalvalue7.png

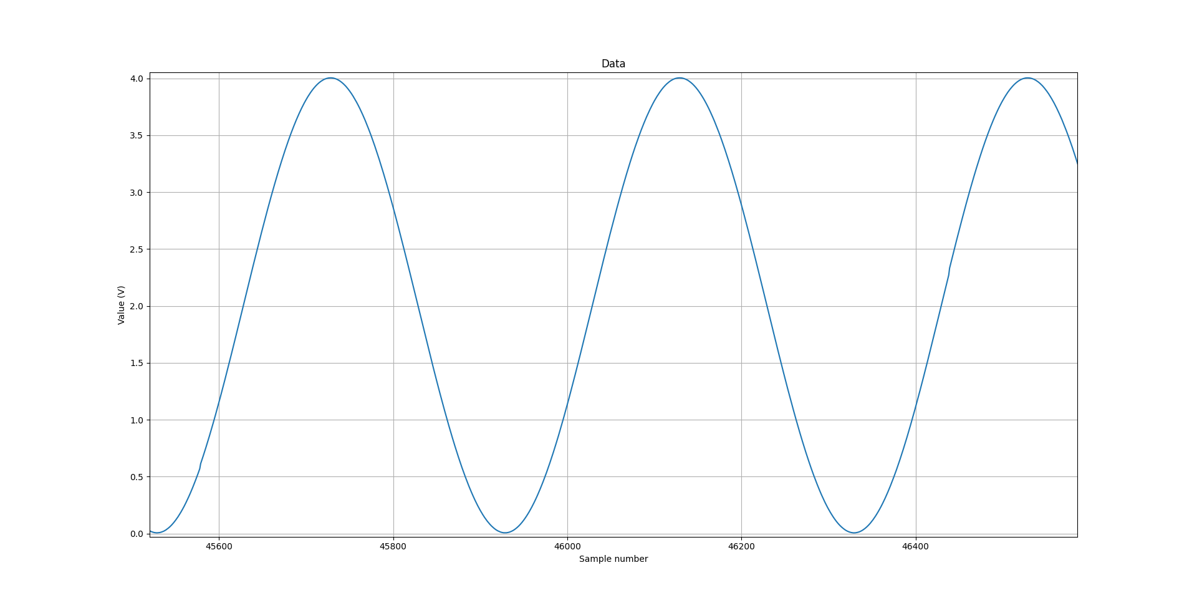
Performance/Sinusoidal/sinusoidalvalue7.png
