mrheltic/Logger/Performance/Sinusoidal/sinusoidalvalue8.png

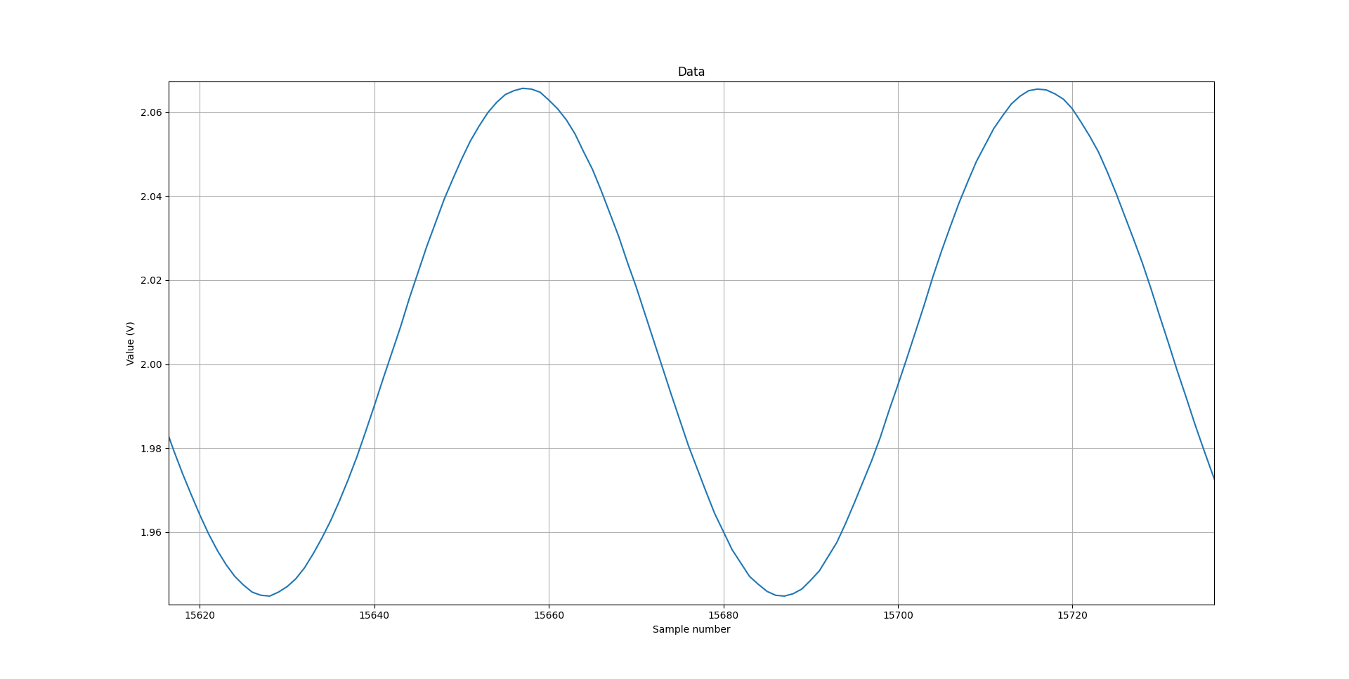
Performance/Sinusoidal/sinusoidalvalue8.png
