mrheltic/Logger/Performance/Sinusoidal/sinusoidalvalue9-far.png

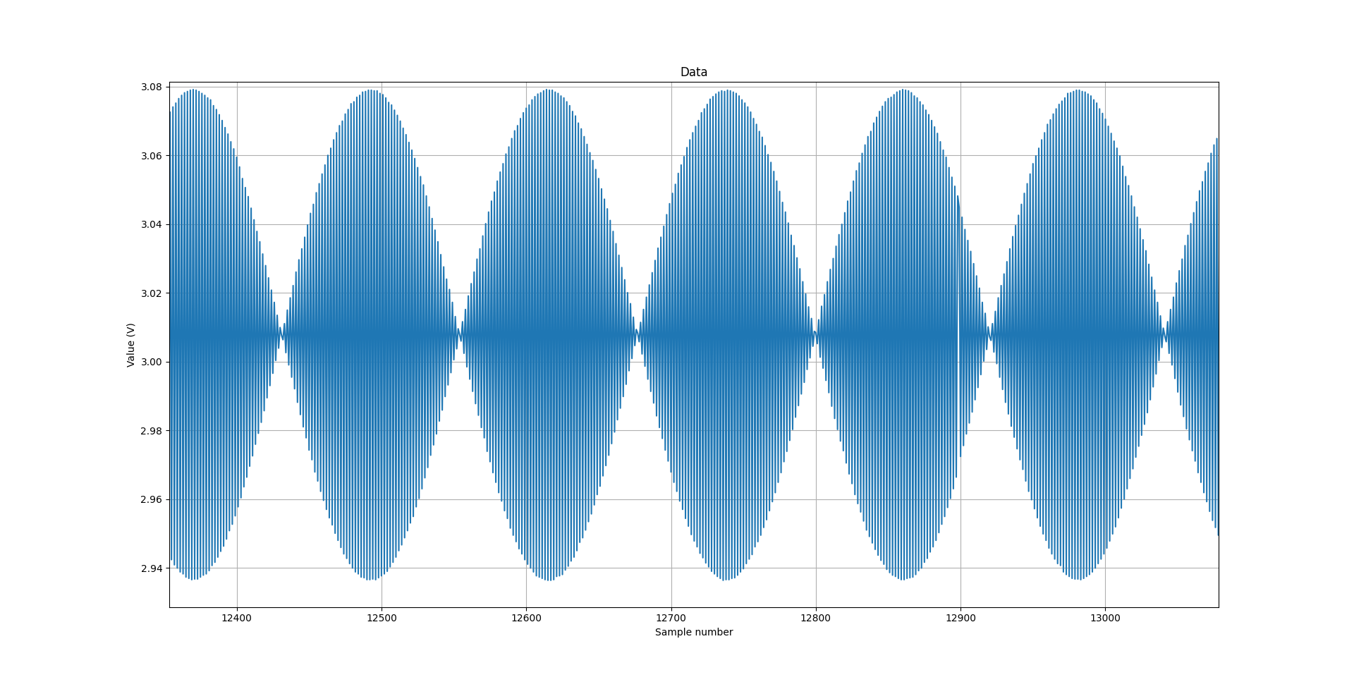
Performance/Sinusoidal/sinusoidalvalue9-far.png
