mrheltic/Logger/Performance/Sinusoidal/sinusoidalvalue9.png

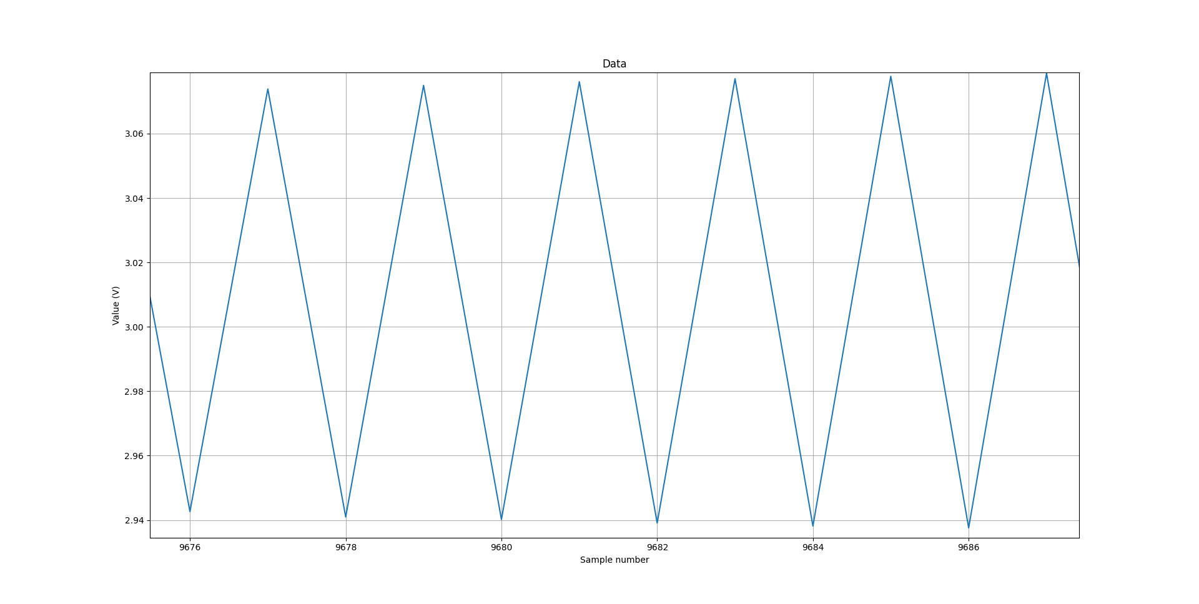
Performance/Sinusoidal/sinusoidalvalue9.png
