mrheltic/Logger/include/controller.h

// controller.h
#ifndef CONTROLLER_H
#define CONTROLLER_H

#include <Arduino.h>
#include "view.h"
#include <Adafruit_ADS1X15.h>
#include <SD.h>
#include "model.h"

// Dichiazione enum
enum MODE
{
    DISPLAY_ONLY=0,
    SD_ONLY=2,
    SERIAL_ONLY=1
};

enum CHANNEL
{
    VOLTAGE=0,
    CURRENT=1,
    RESISTANCE=2
};

// Dichiarazione delle variabili globali
extern MODE currentMode;
extern CHANNEL currentChannel;
extern int currentSampleRate;
extern int scrollFrequency;
extern int scrollDuration;
extern int selectFrequency;
extern int selectDuration;

// Dichiarazione delle funzioni
void initializeSerial();
boolean initializeOutputDevices();
boolean initializeInputDevices();
boolean ADCinitialize();
boolean initializeSDcard();
void logfileSDcard();
void writeFile(fs::FS &fs, const char *path, const char *message);
void appendFile(fs::FS &fs, const char *path, const char *message);
boolean initializeRTC();
boolean initializeDevices();
boolean goUp();
boolean goDown();
boolean select();
void soundBuzzer(int frequency, int duration);
String getTimeStamp();
String getDateStamp();
void loggerActDisplay();
void loggerActSerial();
void loggerActSD();
void outputModeAct();
void inputModeAct();
void infoAct(boolean subSetup);
void sampleSetAct();
void setRate(uint16_t value);
float conversionMeasurement();
float currentFactor();
boolean preliminaryControl();
void adcSetup();
void setChannel(CHANNEL channel);
#endif // CONTROLLER_H
