mrheltic/Logger/src/view.cpp

#include <Adafruit_SSD1306.h>
#include <Adafruit_GFX.h>
#include <Wire.h>

#include "../include/controller.h"
#include "../include/view.h"

#define OLED_RESET -1 // probably, shares the RST with ESP32

// DECLARING VARIABLES FOR SCREEN
#define SCREEN_WIDTH 128
#define SCREEN_HEIGHT 64

// MENU INTERFACE
//  'Menu_1', 128x64px
static const unsigned char PROGMEM bitmap_Menu_1[] = {
    0x00, 0x00, 0x00, 0x00, 0x00, 0x00, 0x00, 0x00, 0x00, 0x00, 0x00, 0x00, 0x00, 0x00, 0x00, 0x00,
    0x00, 0x00, 0x00, 0x00, 0x00, 0x00, 0x00, 0x00, 0x00, 0x00, 0x00, 0x00, 0x00, 0x00, 0x00, 0x70,
    0x00, 0x00, 0x00, 0x00, 0x00, 0x00, 0x00, 0x00, 0x00, 0x00, 0x00, 0x00, 0x00, 0x00, 0x00, 0xf8,
    0x00, 0x00, 0x00, 0x00, 0x00, 0x00, 0x00, 0x00, 0x00, 0x00, 0x00, 0x00, 0x00, 0x00, 0x00, 0xf8,
    0x00, 0x00, 0x00, 0x00, 0x00, 0x00, 0x00, 0x00, 0x00, 0x00, 0x00, 0x00, 0x00, 0x00, 0x00, 0xf8,
    0x07, 0x00, 0x00, 0x00, 0x10, 0x00, 0x00, 0x00, 0x00, 0x00, 0x00, 0x00, 0x00, 0x00, 0x00, 0xf8,
    0x08, 0x80, 0x00, 0x00, 0x10, 0x00, 0x00, 0x00, 0x40, 0x00, 0x00, 0x00, 0x00, 0x00, 0x00, 0xf8,
    0x08, 0x0e, 0x3b, 0x1e, 0x10, 0xe0, 0x1c, 0x38, 0xf0, 0x00, 0x00, 0x00, 0x00, 0x00, 0x00, 0xf8,
    0x08, 0x11, 0x24, 0x91, 0x11, 0x10, 0x22, 0x44, 0x40, 0x00, 0x00, 0x00, 0x00, 0x00, 0x00, 0xf8,
    0x07, 0x01, 0x24, 0x91, 0x11, 0x10, 0x20, 0x44, 0x40, 0x00, 0x00, 0x00, 0x00, 0x00, 0x00, 0xf8,
    0x00, 0x8f, 0x24, 0x91, 0x11, 0xf0, 0x1c, 0x7c, 0x40, 0x00, 0x00, 0x00, 0x00, 0x00, 0x00, 0xf8,
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
    0x00, 0x24, 0x40, 0x00, 0x24, 0x40, 0x00, 0x24, 0x40, 0x00, 0x27, 0xc0, 0x00};
// '10_6', 20x15px
const unsigned char bitmap_10_6[] PROGMEM = {
    0x00, 0x00, 0x00, 0x00, 0x01, 0xc0, 0x00, 0x01, 0x00, 0x00, 0x01, 0x00, 0x00, 0x01, 0xc0, 0x27,
    0xc1, 0x40, 0x24, 0x41, 0x40, 0x24, 0x41, 0xc0, 0x24, 0x40, 0x00, 0x24, 0x40, 0x00, 0x24, 0x40,
    0x00, 0x24, 0x40, 0x00, 0x24, 0x40, 0x00, 0x24, 0x40, 0x00, 0x27, 0xc0, 0x00};
// 'ampere', 16x16px
const unsigned char bitmap_ampere[] PROGMEM = {
    0x00, 0x00, 0x00, 0x00, 0x00, 0x00, 0x0e, 0x3a, 0x1b, 0x2a, 0x31, 0xae, 0x31, 0x80, 0x31, 0x86,
    0x3f, 0x88, 0x3f, 0x9e, 0x31, 0x80, 0x31, 0x92, 0x31, 0x92, 0x31, 0x8c, 0x00, 0x00, 0x00, 0x00};
// 'display', 16x16px
const unsigned char bitmap_display[] PROGMEM = {
    0x00, 0x00, 0x7f, 0xfe, 0x40, 0x02, 0x5c, 0x02, 0x58, 0x02, 0x50, 0x02, 0x40, 0x02, 0x40, 0x02,
    0x40, 0x02, 0x40, 0x02, 0x7f, 0xfe, 0x03, 0xc0, 0x03, 0xc0, 0x07, 0xe0, 0x1f, 0xf8, 0x00, 0x00};
// 'ohm', 16x16px
const unsigned char bitmap_ohm[] PROGMEM = {
    0x00, 0x00, 0x00, 0x00, 0x00, 0x00, 0x00, 0x3e, 0x00, 0x2a, 0x1c, 0x2a, 0x22, 0x00, 0x41, 0x06,
    0x41, 0x08, 0x41, 0x1e, 0x22, 0x00, 0x14, 0x12, 0x77, 0x12, 0x00, 0x0c, 0x00, 0x00, 0x00, 0x00};
// 'sd_card', 16x16px
const unsigned char bitmap_sd_card[] PROGMEM = {
    0x00, 0x00, 0x07, 0xf8, 0x0a, 0xa8, 0x12, 0xa8, 0x12, 0xa8, 0x10, 0x08, 0x10, 0x08, 0x16, 0xc8,
    0x14, 0xa8, 0x16, 0xa8, 0x12, 0xa8, 0x16, 0xc8, 0x10, 0x08, 0x10, 0x08, 0x1f, 0xf8, 0x00, 0x00};
// 'volt', 16x16px
const unsigned char bitmap_volt[] PROGMEM = {
    0x00, 0x00, 0x00, 0x00, 0x00, 0x00, 0x31, 0x9e, 0x31, 0x92, 0x31, 0x9e, 0x31, 0x80, 0x31, 0x86,
    0x31, 0x88, 0x31, 0x9e, 0x31, 0x80, 0x3b, 0x92, 0x1f, 0x12, 0x0e, 0x0c, 0x00, 0x00, 0x00, 0x00};
// 'wifi', 16x16px
const unsigned char bitmap_usb[] PROGMEM = {
    0x00, 0x00, 0x0f, 0xf0, 0x08, 0x10, 0x0a, 0x50, 0x0a, 0x50, 0x08, 0x10, 0x08, 0x10, 0x1f, 0xf8,
    0x10, 0x08, 0x10, 0x08, 0x10, 0x08, 0x10, 0x08, 0x08, 0x10, 0x07, 0xe0, 0x01, 0x80, 0x01, 0x80};

Adafruit_SSD1306 display(SCREEN_WIDTH, SCREEN_HEIGHT, &Wire, OLED_RESET); // declaring display object

/**
 * @brief Initializes the screen.
 *
 * @return true if the screen is successfully initialized, false otherwise.
 */
boolean initializeScreen()
{
  if (!display.begin(SSD1306_SWITCHCAPVCC, 0x3C))
  {
    Serial.println(F("SSD1306 allocation failed"));
    return false;
  }
  display.clearDisplay();
  display.display();
  return true;
}

/**
 * @brief Updates the context cursor position on the display.
 *
 * @param position The position of the cursor. Valid values are 0, 1, and 2.
 */
void updateContextCursor(int position)
{
  switch (position)
  {
  case 0:
    display.drawBitmap(2, 22, bitmap_cursor, 122, 20, 1);

    break;
  case 1:
    display.drawBitmap(2, 44, bitmap_cursor, 122, 20, 1);
    break;
  case 2:
    display.drawBitmap(2, 1, bitmap_cursor, 122, 20, 1);

    break;
  }
}

/**
 * @brief Updates the menu with the specified value.
 *
 * @param menu The value to update the menu with.
 * @return The updated menu value.
 */
int updateMenu(int menu)
{
  // display.display();
  display.clearDisplay();
  switch (menu)
  {
  case 0:
    menu = 5;
    updateMenu(menu);
    break;
  case 1:
    display.drawBitmap(0, 0, bitmap_Menu_1, 128, 64, WHITE);
    display.display();
    break;
  case 2:
    display.drawBitmap(0, 0, bitmap_Menu_2, 128, 64, WHITE);
    display.display();
    break;
  case 3:
    display.drawBitmap(0, 0, bitmap_Menu_3, 128, 64, WHITE);
    display.display();
    break;
  case 4:
    display.drawBitmap(0, 0, bitmap_Menu_4, 128, 64, WHITE);
    display.display();
    break;
  case 5:
    display.drawBitmap(0, 0, bitmap_Menu_5, 128, 64, WHITE);
    display.display();
    break;
  case 6:
    menu = 1;
    updateMenu(menu);
    break;
  }
  return menu;
}

/**
 * Displays an error message graphic on the display based on the current mode.
 *
 * @param currentMode The current mode indicating the type of error.
 *                    1 for Wi-Fi error, 0 for SD card error.
 */
void errorMessageGraphic(int currentMode)
{
  display.clearDisplay();
  if (currentMode == 1)
    display.drawBitmap(0, 0, bitmap_error_serial, 128, 64, WHITE);
  else
    display.drawBitmap(0, 0, bitmap_error_sdcard, 128, 64, WHITE);
  display.display();
}

/**
 * @brief Displays a waiting animation on the screen while waiting for serial communication.
 */
void waitSerialGraphic()
{
  display.clearDisplay();
  display.drawBitmap(0, 0, bitmap_waiting_serial, 128, 64, WHITE);
  display.display();
}

// Submenu graphics
/**
 * @brief Displays the logger graphic based on the specified mode and channel.
 *
 * @param mode The mode of the logger.
 * @param channel The channel of the logger.
 */

void loggerGraphic(String currentTime, float measure)
{
  display.clearDisplay();
  display.drawBitmap(0, 0, bitmap_logger, 128, 64, WHITE);

  if (abs(measure) < 0.005)
    measure = abs(measure);

  display.setCursor(0, 0);
  display.setTextSize(1);
  display.setTextColor(WHITE);
  display.setCursor(24, 54);
  display.println(currentTime);
  display.setCursor(0, 0);

  switch (currentMode)
  {
  case DISPLAY_ONLY:
    display.drawBitmap(0, 16, bitmap_display, 16, 16, WHITE);
    printMeasureValue(measure);
    break;
  case SERIAL_ONLY:
    display.drawBitmap(0, 16, bitmap_usb, 16, 16, WHITE);
    display.drawBitmap(17,0, bitmap_USB_connection, 111, 47, WHITE);
    printBitmapIcon();
    break;
  case SD_ONLY:
    display.drawBitmap(0, 16, bitmap_sd_card, 16, 16, WHITE);
    display.drawBitmap(17,0, bitmap_SD_connection, 111, 47, WHITE);
    printBitmapIcon();
    break;
  }

  display.display();
}

void printBitmapIcon(){
  switch (currentChannel)
    {
    case VOLTAGE:
      display.drawBitmap(0, 32, bitmap_volt, 16, 16, WHITE);
      break;
    case CURRENT:
      display.drawBitmap(0, 32, bitmap_ampere, 16, 16, WHITE);
      break;
    case RESISTANCE:
      display.drawBitmap(0, 32, bitmap_ohm, 16, 16, WHITE);
      break;
    }
}

void printMeasureValue(float measure){
  switch (currentChannel)
    {
    case VOLTAGE:
      display.setTextSize(1);
      display.setCursor(23, 0);
      display.print("0-26V  Mean Value");
      display.drawBitmap(0, 32, bitmap_volt, 16, 16, WHITE);
      display.setTextSize(3);
      display.setTextColor(WHITE);
      display.setCursor(30, 20);
      display.println(measure);
      break;
    case CURRENT:
      display.setTextSize(1);
      display.setCursor(67, 0);
      display.print("RMS Value");
      display.drawBitmap(0, 32, bitmap_ampere, 16, 16, WHITE);
      display.setTextSize(3);
      display.setTextColor(WHITE);
      display.setCursor(30, 20);
      display.println(measure);
      break;
    case RESISTANCE:
      display.setTextSize(1);
      display.setCursor(59, 0);
      display.print("Mean Value");
      display.drawBitmap(0, 32, bitmap_ohm, 16, 16, WHITE);
      display.setTextSize(2);
      display.setTextColor(WHITE);

      display.setCursor(26, 28);

      if (abs(measure) >= 10000000)
      {
        display.drawBitmap(17, 0, bitmap_inf, 110, 47, WHITE);
      }
      else if (abs(measure) >= 1000000)
      {
        display.println(measure / 1000000);
        display.drawBitmap(105, 26, bitmap_10_6, 20, 15, WHITE);
      }
      else if (abs(measure) >= 1000)
      {
        display.println(measure / 1000);
        display.drawBitmap(105, 26, bitmap_10_3, 20, 15, WHITE);
      }
      else if (abs(measure) < 1000 && abs(measure) > 20)
      {
        display.println(measure);
      }
      else
      {
        display.drawBitmap(17, 0, bitmap_short, 110, 47, WHITE);
      }

      break;

    default:
      break;
    }
}

/**
 * @brief Outputs the graphic mode based on the given mode.
 *
 * @param mode The mode to be displayed.
 */
void outputModeGraphic(int channel)
{
  display.clearDisplay();
  display.drawBitmap(0, 0, bitmap_Output_mode, 128, 64, WHITE);
  updateContextCursor(channel);
  display.display();
}

/**
 * Sets the input mode for the graphic display.
 *
 * @param mode The input mode to be set.
 */
void inputModeGraphic(int mode)
{
  display.clearDisplay();
  display.drawBitmap(0, 0, bitmap_Input_mode, 128, 64, WHITE);
  updateContextCursor(mode);
  display.display();
}

/**
 * @brief Displays an information graphic based on the state of various components.
 *
 * @param WifiState The state of the WiFi component.
 * @param sdState The state of the SD card component.
 * @param RTCState The state of the RTC (Real-Time Clock) component.
 */
void infoGraphic(String TimeStamp, String DateStamp)
{
  // String wifiStateString = "connected";
  // String SDCardStateString = "detected";
  // String RTCStateString = "initializide";
  String versionFirmware = "-v2.4.3";

  display.clearDisplay();
  display.setTextSize(1);
  display.setTextColor(SSD1306_WHITE);
  display.setCursor(1, 2);
  display.print(F("Firmware:  "));
  display.println(versionFirmware);
  display.setCursor(1, 18);
  display.print(F("Time: "));
  display.println(TimeStamp);
  display.setCursor(1, 34);
  display.print(F("Date: "));
  display.println(DateStamp);
  display.setCursor(1, 50);
  display.print(F("Battery: "));
  display.println("89%");
  display.display();
}

/**
 * @brief Sets the graphic for the given sample.
 *
 * This function sets the graphic representation for the specified sample.
 *
 * @param sample The sample number.
 */
void sampleSetGraphic(int sample)
{
  display.clearDisplay();
  display.drawBitmap(0, 0, bitmap_sample_rate_set, 128, 64, WHITE);
  display.setTextColor(WHITE);
  display.setTextSize(3);
  display.setCursor(22, 16);
  display.print(sample);
  display.display();
}

/**
 * @brief Controls the graphic representation of the sample set selector.
 *
 * @param arrowup Indicates whether the arrow should point up or down.
 */
void sampleSetSelectorGraphic(boolean arrowup)
{
  display.clearDisplay();
  display.drawBitmap(0, 0, bitmap_sample_rate_set, 128, 64, WHITE);
  if (arrowup == 0)
  {
    display.drawBitmap(87, 28, bitmap_down_sample, 32, 17, WHITE);
  }
  else
  {
    display.drawBitmap(87, 8, bitmap_up_sample, 32, 17, WHITE);
  }
  display.display();
}
